looaeedr/whd/logs/preflight/20260906_t1_assembly_placement_evidence.md

SKILL_EXECUTED: phase6-corner-3d-model-integrity
READ_REFERENCE: 個人AI檔案庫/第二層_專案與SOP/06_踩坑記錄與防錯經驗庫.md
READ_REFERENCE: 基準檔/截角資料庫/README_母規則說明.md
READ_REFERENCE: 基準檔/截角資料庫/certified_relief_rules.json
READ_REFERENCE: 個人AI檔案庫/踩坑庫/phase6_assembly_relief_pitfalls.md
NOTE: T1 authoritative assembly placement contract for divider and inner door.
