looaeedr/whd/.scratch/engineering-drawing-dxf-qa/checkpoints/T3.md

# T3 Checkpoint — Canonical Annotation Planner

- ticket: #58
- branch: `feat/engineering-drawing-dxf-qa`
- tested_head: `b787f8ce18c895f643e5a339e7e7a9ddaff7f10e`
- final_remote_run: `34248282222`
- result: **6 PASS / 0 FAIL / 2.33s**
- preflight: PASS
- config.ini invariant: PASS

## Production
- `ae_engine/drawing_annotations.py`
- `ae_engine/sheetmetal_drawing.py` — preserves `ResolvedCircle.source_type`

## Test
- `tests/test_drawing_annotations.py`

## Contracts locked
- overall dimensions = Final Material bounds
- authoritative resolved-hole metadata reaches planner
- chamfer/relief measured from Final Material
- R only from stable sampled circular runs; no three-point guessing
- deterministic / immutable AnnotationPlan
- annotation does not own CUTTING/BEND/material
