looaeedr/whd/tests_analysis.md

---
whd_doc_role: REFERENCE
whd_contract: project-reference
whd_canonical: null
whd_schema: WHD_DOC_META_V1
---
# TESTS 無用性分析報告

> 運行結果：**17 failed / 402 passed**（共 57 個測試檔，419 個 test case，歷時 166 秒）

---

## 一、🔴 失敗中的「過時規格測試」（最無用）

這類測試描述的是**已不存在的 GUI 設計或已廢棄的 API 行為**，
測試本身「曾經正確」，但現在程式碼已改動，測試成了舊規格的幽靈。

### 1. `test_separate_3d_entry_contract.py` — 2 個失敗

| 測試名稱 | 失敗原因 |
|---|---|
| `test_workspace_keeps_flat_part_buttons_without_dropdown` | `workspace_part_buttons`、`workspace_part_grid` 已不存在於 gui.py |
| `test_workspace_modes_are_part_and_holes_only` | `if mode not in {"part", "holes"}` 字串已不在 gui.py |

**判斷**：測試的是已被重構掉的 workspace 設計，屬於**過期的架構合規測試**，應該刪除或更新。

---

### 2. `test_original_fold_designer_gui_integration.py` — 4 個失敗

| 測試名稱 | 失敗原因 |
|---|---|
| `test_main_gui_has_original_fold_designer_entry_and_snapshot_bridge` | `assert "corner_state" not in snap` 失敗，現在 snapshot **確實帶有** `corner_state` |
| `test_designer_result_only_writes_existing_phase6_numeric_data_and_profile_state` | 同上，寫回邏輯已更改 |
| `test_designer_endcap_result_updates_all_authoritative_endcap_vars_and_part_spec` | 邏輯改變 |
| `test_designer_apply_reloads_current_baseline_without_restoring_baseline_defaults` | 邏輯改變 |

**判斷**：測試的是 fold_designer snapshot 合約的舊版定義。snapshot 現在多了 `corner_state` / `corner_pair_same` 等欄位，這是**刻意擴充**，不是 bug，測試需要更新。

---

### 3. `test_original_fold_designer_bridge.py` — 4 個失敗

| 測試名稱 | 失敗原因 |
|---|---|
| `test_fixed_dwd_bending_ui_keeps_original_input_grid_and_disables_only_dwd_delete` | grid_slaves 中的 label 文字格式已改，`core` 標籤不再以 `str(seg["core"])` 開頭呈現 |
| `test_door_fold_edits_return_to_phase6_snapshot_without_changing_renderer_class` | `out["door_fold_l"]` 期望 23，實際 21，回寫邏輯已改 |
| `test_head_tail_preview_keeps_original_renderer_orientation` | `Poly3DCollection._vec` 屬性在新版 matplotlib 已不存在 |
| `test_head_xy_edits_export_authoritative_endcap_values_without_box_body_overwrite` | `out["fw"]` 期望 30，實際 26，映射邏輯已改 |

**判斷**：
- `_vec` 屬性問題是**第三方庫版本差異**，測試本身在 API 上假設了內部實作細節，高脆弱性。
- 其他三個是邏輯改變後測試未同步更新。

---

### 4. `test_phase6_settings_center_gui_contract.py` — 1 個失敗

| 測試名稱 | 失敗原因 |
|---|---|
| `test_apply_verifier_requires_settings_module_without_banning_corner_comboboxes` | 嘗試讀取 `apply_fold_designer_outside_dims_phase6_fix13.py`，**該檔案已不存在** |

**判斷**：測試依賴的 helper script 已刪除，這是**孤兒測試（orphan test）**，無對應實作可測。

---

### 5. `test_multi_door_gui.py` — 6 個失敗

| 測試名稱 | 失敗原因 |
|---|---|
| `test_multi_door_export_keeps_indicator_settings_owned_by_their_cell` | `BoxCalculatorGUI` 無 `add_workspace_part` 方法 |
| `test_indicator_box_and_small_door_are_same_level_workspace_parts` | `tab_indicator_box` 未加入 notebook |
| `test_single_door_indicator_box_toggle_does_not_change_multi_door_cell_modes` | 同上 |
| `test_single_door_indicator_enable_disables_indicator_box_but_keeps_box_tab_visible` | 同上 |
| `test_multi_door_editor_indicator_commit_does_not_toggle_single_door_global_mode` | `add_workspace_part` 不存在 |
| `test_indicator_box_and_small_door_are_shared_workspace_parts_and_still_in_door_editor` | 同上 |

**判斷**：測試針對 `indicator_box` 的動態 workspace 架構（`add_workspace_part`、動態 tab）撰寫，但 GUI **尚未實作這套機制**，或機制已改變。這些是**超前於實作的規格測試（spec-ahead tests）**。

---

## 二、🟡 「過度字串綁定」測試（脆弱但尚在通過）

這類測試通過 `assert '某段程式碼字串' in gui.py` 來驗證 GUI 實作，
雖然現在還通過，但**極其脆弱**：任何重構、改名、換行都會讓它無故失敗。

| 測試檔 | 問題 |
|---|---|
| `test_gui_scene_data_contract.py` | grep `gui.py` 中特定 token |
| `test_all_panel_hole_entrypoints.py` | grep `gui.py` 函式段落 |
| `test_hole_editor_ux_contract.py` | grep `gui.py` UI label 文字 |
| `test_unified_hole_catalog_contract.py` (部分) | grep `gui.py` 函式段落 |
| `test_separate_3d_entry_contract.py` (第一個) | grep gui.py — 目前通過 |
| `test_startup_door_layout_staticmethod.py` | AST parse gui.py 確認 staticmethod |
| `test_reference_axis_grouping.py` (第三個) | grep gui.py 中的 widget 名稱 |

**判斷**：這些「程式碼考古學測試」可以在不改任何功能的情況下意外失敗，維護成本高，**建議轉成行為驗證或整合測試**。

---

## 三、🟢 真正有價值的測試（保留）

### 核心幾何引擎
- `test_sheetmetal_geometry.py` — Vec2, Polygon 等幾何基礎
- `test_sheetmetal_features.py` — Feature 解析與轉換
- `test_sheetmetal_drawing.py` — DXF primitive 構建
- `test_strip_fold_chain.py` — BEND 位置數學
- `test_four_side_flange_geometry.py` — FourSideFlange
- `test_corner_types.py` — CornerType snapshot regression

### 零件適配器
- `test_sheetmetal_part_adapters.py` — 門、封頭尾、底板適配
- `test_multi_door_layout.py` — 多門尺寸計算邏輯
- `test_endcap_head_mirror.py` — 封頭鏡像

### DXF 輸出管線
- `test_ae_dispatcher.py` — `_build_*_scene` 各零件
- `test_manufacturing_api.py` — generate_part 整合
- `test_manufacturing_policy_boundary.py` — Policy 注入
- `test_manufacturing_api_finished_face_contract.py`
- `test_corner_type_headless.py` — 無 GUI 的 corner type 輸出

### 孔洞系統
- `test_hole_catalog.py`
- `test_hole_rotation.py`
- `test_unified_hole_reference.py`
- `test_feature_surface.py`
- `test_unified_hole_process_toggle.py`
- `test_profile_layer_preservation.py`
- `test_round_hole_pattern.py`

### 架構合規（仍有效）
- `test_clean_break_layout.py` — 確認無舊根目錄模組
- `test_ae_engine_package.py` — 確認 ae_engine 套件完整性

---

## 四、總結建議

| 分類 | 數量 | 建議 |
|---|---|---|
| 🔴 **立即可刪除 / 應更新**（失敗中的過期測試） | ~17 個 case | 更新或刪除 |
| 🟡 **脆弱字串綁定測試**（通過但易斷） | ~10 個 case | 重構為行為測試 |
| 🟢 **真正有價值** | ~392 個 case | 保留 |

### 最優先處理的 3 個動作
1. **刪除** `test_phase6_settings_center_gui_contract.py::test_apply_verifier_requires_settings_module_without_banning_corner_comboboxes`（依賴已不存在的檔案）
2. **更新** `test_original_fold_designer_gui_integration.py` 前兩個失敗測試（snapshot 合約已合法擴充）
3. **評估** `test_multi_door_gui.py` 的 `indicator_box` 系列 —— 若 `add_workspace_part` 機制尚未實作，這些測試是 **spec-ahead**，應先暫時 `@pytest.mark.xfail` 或移至 backlog

## Headless / Xvfb 測試判讀規則（CURRENT）

1. 無 `DISPLAY`：pure/headless tests 必須跑；GUI/Tk tests 應 SKIP，不得把缺 display 的 `TclError` 當功能紅燈。
2. 有 Xvfb：GUI/Tk tests 必須真的執行；任何 geometry/state/save-reload failure 都是有效紅燈，不能以 headless skip 掩蓋。
3. 新 GUI tests 使用 `@pytest.mark.requires_tk_display`。中央兼容層只辨識「缺 DISPLAY」的 Tk `TclError`，不吞其他 TclError。
4. Release gate 必須同時保留 headless 與 Xvfb 證據；只跑其中一種不得宣稱正式 GUI release 通過。
