looaeedr/whd/.scratch/engineering-drawing-dxf-qa/T1.state.md

# T1 State
- task_id: engineering-drawing-dxf-qa
- ticket: #57
- role: QA Accepted
- branch: feat/engineering-drawing-dxf-qa
- baseline_sha: 55541aaef49c3bb5649f52160a87a2834c1072a9
- requirement_red_run_id: 34244926280
- requirement_red_head_sha: 9f92663f1554d93c7af462db89d3283825f6d5f4
- requirement_red_result: 2 failed / valid requirement RED
- final_green_run_id: 34246080067
- final_tested_head_sha: e1eac5a16258f15f805468362390f30020ad6fff
- final_green_result: 8 passed / 0 failed / 1.15s
- config_ini_invariant: PASS
- py_compile: PASS
- cleanup_head_sha: 58ac96e403d8ad43fefa494a8396620f45dfdeca
- workflow_cleanup: PASS / .github/workflows/t1-dxf-acceptance.yml removed
- drift_audit: PASS / production+test blobs identical tested-head→cleanup-head
- status: ACCEPTED
- completed: independent saved-DXF verifier; layer mismatch; CUTTING mismatch; hole/extra geometry checks; public manufacturing seam; AI Library writeback; focused remote QA; workflow cleanup; drift audit
- blocked: none
- production_files: ae_engine/dxf_acceptance.py; ae_engine/manufacturing_api.py
- test_files: tests/test_dxf_acceptance.py; tests/test_resolved_manufacturing_export.py
