looaeedr/whd/.scratch/engineering-drawing-dxf-qa/T2.state.md

# T2 State
- task_id: engineering-drawing-dxf-qa
- ticket: #59
- role: T2 Implementer -> QA Review
- branch: feat/engineering-drawing-dxf-qa
- baseline_sha: 65d34a6b2a43c12bf415a5f2f1e87a270e4c751a
- blocker: #57 CLOSED / ACCEPTED
- requirement_red_run_id: 34246552158
- requirement_red_result: 3 failed / 8 passed / valid R4 RED
- final_green_run_id: 34246933143
- final_green_tested_head_sha: 065bd0b54fbe47cc12908e128235bcb5b163052a
- final_green_result: 11 passed / 0 failed / py_compile PASS / config.ini invariant PASS
- workflow_cleanup_sha: 45ac45bf2b18fa01c19b845a726ab7bca30b9d97
- checkpoint_path: .scratch/engineering-drawing-dxf-qa/checkpoints/T2.md
- status: ACCEPTED
- completed: stable physical IDs; group reopen verifier; missing/extra file-set detection; filename identity policy; AI Library writeback; terminal remote QA; workflow cleanup
- pending: none
- blocked: none
- resume_command: inspect #59 and checkpoint T2.md
- drift_audit: PASS / tested head 065bd0b54fbe47cc12908e128235bcb5b163052a → pre-close head 92923c63036cc85d88bdc6bf400a9e9e318cf501; 5 production/test blobs identical
