looaeedr/whd/.scratch/engineering-drawing-dxf-qa/T3.state.md

# T3 State
- task_id: engineering-drawing-dxf-qa
- ticket: #58
- role: T3 Implementer -> QA Review
- branch: feat/engineering-drawing-dxf-qa
- baseline_sha: 2dc2103eb872c377a3e28ea4ed57907d1e004382
- requirement: R1 canonical Annotation Planner
- valid_requirement_red_run_id: 34247464567
- valid_requirement_red_head_sha: 98e03ac2e91c974057c1b39ac0559b7830334625
- valid_requirement_red_result: 4 failed / explicit R1 assertions
- radius_red_run_id: 34247880052
- radius_red_head_sha: 2cb4e58a72f4a3e4ac703ff1d9a69cd38db7b0fd
- radius_red_result: 1 failed / 4 passed
- metadata_red_run_id: 34248187080
- metadata_red_head_sha: aa49bae8cbea51daa507f59a2aac737f6e83e33d
- metadata_red_result: 1 failed / 5 passed
- final_green_run_id: 34248282222
- final_tested_head_sha: b787f8ce18c895f643e5a339e7e7a9ddaff7f10e
- final_green_result: 6 passed / 0 failed / 2.33s
- preflight: PASS
- config_ini_invariant: PASS
- status: QA_REVIEW
- completed: overall dimensions from final material; authoritative hole callouts; corner relief callouts; stable R callouts; deterministic/immutable plan; ResolvedCircle source metadata preservation; AI Library writeback; final remote QA terminal success
- pending: workflow cleanup readback; drift audit; owning Issue terminal evidence / close
- blocked: none
- production_files: ae_engine/drawing_annotations.py; ae_engine/sheetmetal_drawing.py
- test_file: tests/test_drawing_annotations.py
