looaeedr/whd/.scratch/engineering-drawing-dxf-qa/T4.preflight.evidence.md

T4 Annotation Collision Resolver preflight evidence
phase6-corner-3d-model-integrity
tdd
diagnosing-bugs
monitoring-remote-qa
READ_REFERENCE: 個人AI檔案庫/第二層_專案與SOP/06_踩坑記錄與防錯經驗庫.md
READ_REFERENCE: 個人AI檔案庫/第二層_專案與SOP/04_WHD鈑金展開幾何引擎規範.md
READ_REFERENCE: handoff/04_DEVELOPMENT_RULES.md
READ_REFERENCE: 基準檔/截角資料庫/README_母規則說明.md
READ_REFERENCE: 基準檔/截角資料庫/certified_relief_rules.json
READ_REFERENCE: 個人AI檔案庫/踩坑庫/phase6_assembly_relief_pitfalls.md
