looaeedr/whd/.scratch/engineering-drawing-dxf-qa/T4.state.md

# T4 State
- task_id: engineering-drawing-dxf-qa
- ticket: #60
- role: QA Accepted
- branch: feat/engineering-drawing-dxf-qa
- baseline_sha: 0b4adb92a5fc5fffa8600a0328c7e9255223f21f
- blocker: #58 CLOSED / ACCEPTED
- requirement: R2 deterministic annotation collision resolver
- initial_requirement_red_run_id: 34249387413
- initial_requirement_red_head_sha: 3a89ea5421a7885bb90ffa2529b5de9e4cd83709
- initial_requirement_red_result: 1 failed / explicit missing R2 resolver assertion
- manufacturing_obstacle_red_run_id: 34249693238
- manufacturing_obstacle_red_result: 1 failed / 2 passed
- annotation_text_red_run_id: 34249858548
- annotation_text_red_result: 1 failed / 3 passed
- dimension_line_red_run_id: 34250034870
- dimension_line_red_result: 1 failed / 4 passed
- introduced_bug_run_id: 34250144100
- introduced_bug_classification: INVALID_AS_REQUIREMENT_RED / UnboundLocalError axis-before-assignment
- helper_intermediate_run_id: 34250484170
- helper_intermediate_classification: NON_ACCEPTANCE / helper-only head / 1 failed + 5 passed
- leader_strict_red_run_id: 34250338340
- leader_strict_red_result: 1 failed / 5 passed
- final_green_run_id: 34250724434
- final_tested_head_sha: 4a978507f81c51ff5e54aa4d0c59451ac7ab3823
- final_green_result: 13 passed / 0 failed / 0.63s
- preflight: PASS
- py_compile: PASS / drawing_annotations + drawing_annotation_layout + sheetmetal_drawing
- config_ini_invariant: PASS
- status: ACCEPTED
- completed: deterministic axis-constrained dimensions; CUTTING/BEND/hole obstacle extraction; annotation text/dimension self-avoidance; TITLE/TECH reserved regions; callout leader placement; unresolved diagnostics; strict failure; combined T3+T4 regression; AI Library writeback
- pending: none
- blocked: none
- production_files: ae_engine/drawing_annotation_layout.py
- upstream_guard_files: ae_engine/drawing_annotations.py; ae_engine/sheetmetal_drawing.py
- test_files: tests/test_annotation_collision_resolver.py; tests/test_drawing_annotations.py
- cleanup_head_sha: 7625b8586e08b7c550f9da4f6ee6405f46a0f24f
- workflow_cleanup: PASS / focused workflow removed and remote-read absent
- drift_audit: PASS / 5 production-test blobs identical tested-head→cleanup-head
