looaeedr/whd/.scratch/engineering-drawing-dxf-qa/T5.preflight.evidence.md

T5 2D / Engineering Drawing integration preflight evidence
tdd
diagnosing-bugs
monitoring-remote-qa
READ_REFERENCE: 個人AI檔案庫/第二層_專案與SOP/04_WHD鈑金展開幾何引擎規範.md
READ_REFERENCE: 個人AI檔案庫/第二層_專案與SOP/06_踩坑記錄與防錯經驗庫.md
READ_REFERENCE: handoff/04_DEVELOPMENT_RULES.md
