looaeedr/whd/.scratch/engineering-drawing-dxf-qa/T5.state.md

# T5 State
- task_id: engineering-drawing-dxf-qa
- ticket: #61
- role: QA Accepted
- branch: feat/engineering-drawing-dxf-qa
- baseline_sha: 836de5c2e589dc300c10b0e15220d1e243454fd8
- blockers: #58 CLOSED / #60 CLOSED
- requirement: R1/R2 2D + Engineering Drawing integration
- r1_red_run_id: 34251681198
- r1_red_head_sha: d2182631f89565f3638ef5f0827e70a041cc007e
- r1_red_result: 2 failed / shared Engineering Drawing seam missing + 6/6 primary 2D previews bypass AnnotationPlan
- r1_green_run_id: 34252792624
- r1_green_result: 4 passed / 0 failed
- r2_red_run_id: 34253016841
- r2_red_head_sha: 89de76ef757f405156c234a023f479a173f4cb5f
- r2_red_result: 2 failed / 4 passed / shared finished provider missing + 6/6 2D previews bypass finished summary
- r2_harness_runs: 34253175734, 34253218116, 34253241070, 34253284565, 34253307500
- r2_harness_classification: NON-ACCEPTANCE / matplotlib import dependency in source-ownership test; later heads had 5 passing behavioral guards
- r2_green_run_id: 34253442671
- r2_green_result: 6 passed / 0 failed
- behavior_guard_run_id: 34253559918
- behavior_guard_result: 8 passed / 0 failed
- parity_guard_run_id: 34253660862
- parity_guard_result: SUCCESS
- final_green_run_id: 34253680763
- final_tested_head_sha: 33462e78a282a3999f29abd1a3673a106a78f999
- final_green_result: 22 passed / 0 failed / 4.63s
- preflight: PASS
- py_compile: PASS / planner + collision + engineering projection + display dimensions + 3D view + bridge + GUI
- config_ini_invariant: PASS
- completed: shared AnnotationPlan projection; 6 primary 2D previews integrated; handwritten overall W/H removed; manufacturing DXF separation; shared 2D/3D finished-dimension provider; folded mesh priority; box-body 400x596x250 parity; family-switch stale-ID guard
- ai_library_writeback: DONE
- status: ACCEPTED
- pending: none
- blocked: none
- production_files: ae_engine/engineering_drawing.py; ae_engine/display_dimensions.py; gui.py; fold_designer_bridge.py; phase6_final_scene_view.py
- test_files: tests/test_engineering_drawing_integration.py; tests/test_drawing_annotations.py; tests/test_annotation_collision_resolver.py
- cleanup_head_sha: 1cb592beed4b03031bbe4db08f01cada67d48111
- workflow_cleanup: PASS / focused workflow removed and remote-read absent
- drift_audit: PASS / 10 production-test blobs identical tested-head→cleanup-head
