looaeedr/whd/.scratch/engineering-drawing-dxf-qa/T6.preflight.evidence.md

# T6 Combined Acceptance Preflight Evidence

- task: T6 Combined Acceptance — DXF reopen / multipart Receiving Divider / Vault / Save-Reload / engineering annotation / remote QA
- repository: looaeedr/whd
- branch: feat/engineering-drawing-dxf-qa
- integrated_head: bb8e495983e4c0da27724c0809bb7c52f86ba4b9
- integration_parents: 521a166dc5ef0b002646587a60c373fa95a52818 + b8f08cfbf6fa83617135da70648c946aefe74bd4

READ_SKILL: phase6-corner-3d-model-integrity
READ_SKILL: phase6-overlay-relief-basis
READ_SKILL: diagnosing-bugs
READ_SKILL: tdd
READ_SKILL: monitoring-remote-qa
READ_SKILL: 掃描深模組

READ_REFERENCE: 個人AI檔案庫/第二層_專案與SOP/04_WHD鈑金展開幾何引擎規範.md
READ_REFERENCE: 個人AI檔案庫/第二層_專案與SOP/06_踩坑記錄與防錯經驗庫.md
READ_REFERENCE: handoff/04_DEVELOPMENT_RULES.md
READ_REFERENCE: 基準檔/截角資料庫/README_母規則說明.md
READ_REFERENCE: 基準檔/截角資料庫/certified_relief_rules.json
READ_REFERENCE: 個人AI檔案庫/踩坑庫/phase6_assembly_relief_pitfalls.md
READ_CONTEXT: CONTEXT.md

## Combined hard gates
- T1–T5 terminal evidence already closed/accepted.
- Issue63 accepted production must be present in the same tested branch before Combined.
- Receiving multipart physical pieces are ownership/collision authority.
- Divider fixed-hole source datum comes from 中隔.dxf fixed features, never its outer contour.
- Validation values are not production calculation inputs; no magic 174 / 47-26 / 100 / 1mm / bbox/probe oracle.
- production DXF remains canonical manufacturing scene only.
- Engineering Drawing remains annotation-only downstream projection.
- Save→Reload must preserve canonical state and Final Material.
- config.ini SHA256 must remain identical.
