looaeedr/whd/.scratch/engineering-drawing-dxf-qa/T6.state.md

# T6 State
- task_id: engineering-drawing-dxf-qa
- ticket: #62
- role: QA Accepted
- branch: feat/engineering-drawing-dxf-qa
- original_baseline_sha: 55541aaef49c3bb5649f52160a87a2834c1072a9
- t1_t5_head_before_issue63_merge: 521a166dc5ef0b002646587a60c373fa95a52818
- issue63_closing_head: b8f08cfbf6fa83617135da70648c946aefe74bd4
- integrated_head: bb8e495983e4c0da27724c0809bb7c52f86ba4b9
- integration_commit_type: two-parent merge
- integration_parents: 521a166dc5ef0b002646587a60c373fa95a52818 + b8f08cfbf6fa83617135da70648c946aefe74bd4
- combined_run_id: 34254984310
- combined_tested_head_sha: f39398c1fbd3e50e26b5fc8453729c52bfef135e
- combined_status: completed / success
- core_dxf_annotation: 39 PASS / 0 FAIL
- receiving_issue63_suite: 91 PASS / 0 FAIL
- vault_save_reload: 45 PASS / 0 FAIL
- combined_total: 175 PASS / 0 FAIL
- preflight: PASS
- py_compile: PASS
- source_ownership_guards: PASS
- config_ini_before: 980eab68d4a1732a5313b22329852dfc9691c83e4e2a64cccd18022afae4ee67
- config_ini_after: 980eab68d4a1732a5313b22329852dfc9691c83e4e2a64cccd18022afae4ee67
- config_ini_invariant: PASS
- blockers: #57 CLOSED / #58 CLOSED / #59 CLOSED / #60 CLOSED / #61 CLOSED / #63 CLOSED
- ai_library_writeback: DONE + REREAD
- skill_writeback: phase6-corner-3d-model-integrity DONE + REREAD
- status: ACCEPTED
- pending: none
- blocked: none
- workflow_cleanup: PASS / t6-combined-acceptance.yml removed and remote-read absent
- first_drift_audit_head: 5b515c23ad00194c0b30d7f9393b3dbf0316514c
- first_drift_audit: PASS / only AI-Skill-state-checkpoint-workflow cleanup files changed
- validation_docs_target_head: a26d14f524ff4c094afd4718fc61679db663f847
- validation_docs_merge_head: 9a0acc9315519afbb128d0f8e09c053f336439f1
- validation_docs_merge: PASS / two-parent docs-only merge / production-test drift 0
- target_integration_head: 69ede1f29af9f97b3bed1b844478f40fc251f347
- target_integration: PASS / cleanup/2d-3d-sync non-force fast-forward / remote reread identical
- final_production_test_drift: PASS / 0 files changed after tested head
- tracker_close: PASS / #62 closed
- final_target_head: 34cb7975cc4bad8d0102c52884265739412e8139
