looaeedr/whd/.scratch/validation-authority-boundary/phase6_preflight_evidence.md

# Validation Authority Boundary — Phase6 Preflight Evidence

- task: 驗證只能拿來判定對不對，不能反過來當 production 計算來源；加入 Skill 與 AI Library
- repository: looaeedr/whd
- branch: docs/validation-authority-boundary
- parent: cleanup/2d-3d-sync@b8f08cfbf6fa83617135da70648c946aefe74bd4

READ_SKILL: phase6-release-packaging
READ_SKILL: phase6-corner-3d-model-integrity
READ_SKILL: tdd

READ_REFERENCE: 個人AI檔案庫/第二層_專案與SOP/06_踩坑記錄與防錯經驗庫.md
READ_REFERENCE: release_required_artifacts.json
READ_REFERENCE: 個人AI檔案庫/踩坑庫/phase6_assembly_relief_pitfalls.md

## RED baseline
- phase6-corner-3d-model-integrity explicit "validation is not calculation source": false
- explicit ban on pytest expected/tolerance feeding production: false
- explicit ban on validation measurement backfeed: false

## Scope expansion
- Added general TDD authority boundary after locating the project-wide tdd Skill.

## Intended files
- .agents/skills/engineering/tdd/SKILL.md
- .agents/skills/engineering/phase6-corner-3d-model-integrity/SKILL.md
- 個人AI檔案庫/第二層_專案與SOP/06_踩坑記錄與防錯經驗庫.md
- 個人AI檔案庫/踩坑庫/phase6_assembly_relief_pitfalls.md

## Remote preflight terminal evidence
- run_id: 34254285308
- head_sha: 89f7017726e0f51bbf3ea51c9730beeaf23541a1
- conclusion: completed / success
- report: phase6-release-packaging ✓; global pitfalls ✓; release_required_artifacts.json ✓
- scope-expansion run_id: 34254488598
- head_sha: b1654e7523dd94042e3dd0016cf7745d17482fe7
- conclusion: completed / success

## GREEN content contract
- tdd one-way validation authority: PASS
- phase6-corner-3d-model-integrity validation/calculation boundary: PASS
- global AI Library boundary: PASS
- phase6 assembly/relief AI Library boundary: PASS
- expected/fixture/probe/tolerance backfeed ban: PASS
- independent authoritative provenance requirement: PASS
- production/test source drift: 0 production files, 0 test files

## Closing audit
- one-shot workflow cleanup: PASS
- accidental rerun after workflow deletion: none
- production files changed: 0
- test files changed: 0
- target before integration: cleanup/2d-3d-sync@b8f08cfbf6fa83617135da70648c946aefe74bd4
- pre-evidence closing commit: d747c563e24d0a3f9bddbb03391587461fa15d4b
- integration mode: non-force fast-forward only
