looaeedr/whd/logs/preflight/20260906_remote_qa_monitoring_evidence.md

# Remote QA Monitoring Skill Preflight Evidence

Task: 增加規則：同步遠端 QA 時必須啟動監控技能，並持續追到遠端 QA 終態。
Date: 2026-09-06

READ_SKILL: phase6-release-packaging
READ_SKILL: dispatching
READ_SKILL: monitoring-remote-qa
READ_REFERENCE: 個人AI檔案庫/第二層_專案與SOP/06_踩坑記錄與防錯經驗庫.md
READ_REFERENCE: .agents/skills/skill_registry.json
READ_REFERENCE: tools/phase6_skill_preflight.py
READ_REFERENCE: release_required_artifacts.json

Planned files:
-  .agents/skills/engineering/monitoring-remote-qa/SKILL.md
-  .agents/skills/engineering/monitoring-remote-qa/agents/openai.yaml
- .agents/skills/skill_registry.json
- .agents/skills/engineering/派工/SKILL.md
- .agents/skills/engineering/README.md
- AGENTS.md

RESULT: PRE-FLIGHT READ COMPLETE
POST-CREATE READBACK: monitoring-remote-qa SKILL.md verified

REMOTE QA CONTRACT: 22 PASS / 0 FAIL (run 34022265417)
ROUTE/WIRING CHECK: PASS (run 34022430582)
CANONICAL SKILL: monitoring-remote-qa
TEMP SELF-TEST WORKFLOW: removed
