looaeedr/whd/logs/preflight/20260906_remote_qa_monitoring_skill_evidence.md

# Remote QA Monitoring Skill Preflight Evidence

READ_SKILL: phase6-release-packaging
READ_SKILL: diagnosing-bugs
READ_SKILL: tdd
READ_SKILL: monitoring-remote-qa
READ_SKILL: superpowers/writing-skills
READ_SKILL: superpowers/test-driven-development
READ_REFERENCE: 個人AI檔案庫/第二層_專案與SOP/06_踩坑記錄與防錯經驗庫.md
READ_REFERENCE: release_required_artifacts.json
RED: tests/test_remote_qa_monitoring_skill_contract.py -> 1 failed (skill missing)
GREEN: tests/test_remote_qa_monitoring_skill_contract.py -> 1 passed
PREFLIGHT: PASS
