looaeedr/whd/logs/preflight/20260906_t10_release_verification_evidence.md

# T10 Release Verification Evidence

phase6-corner-3d-model-integrity
phase6-release-packaging
diagnosing-bugs
tdd
dispatching
READ_REFERENCE: 個人AI檔案庫/第二層_專案與SOP/06_踩坑記錄與防錯經驗庫.md
READ_REFERENCE: 基準檔/截角資料庫/README_母規則說明.md
READ_REFERENCE: 基準檔/截角資料庫/certified_relief_rules.json
READ_REFERENCE: 個人AI檔案庫/踩坑庫/phase6_assembly_relief_pitfalls.md
READ_REFERENCE: release_required_artifacts.json

## Scope
- Issue: #10 高風險完整 Headless + GUI Gate / Release Verification
- T10 start commit: 60fb7a935cd078c38e81d5ad6175fa42b0cc66ce
- Execution tree SHA: 51c1454ea64284f204c286c3876e92b2ff4daa1d
- Backup: backup-20260906-110833
- Headless journal: logs/release_gate/t10_phase6_headless.jsonl
- Xvfb journal: logs/release_gate/t10_phase6_xvfb.jsonl

## Durable Release Gate
- Collection count: 1473 nodeids in both modes.
- Collection SHA256: 14db2438f4285b64eb396a5744986104a02a9135cfcefcfbb12de72ecaeb269c.
- Headless: completed=1473, passed=1194, skipped=279, failed_batches=0, pending=0, teardown_timeout_batches=0.
- Xvfb: completed=1473, passed=1473, skipped=0, failed_batches=0, pending=0, teardown_timeout_batches=2.
- Xvfb aggregate timeout records: 4; every timed-out nodeid was later recorded complete in the same durable journal; unresolved timeout nodeids=0.
- The 2 complete_teardown_timeout batches each have full `20 passed` pytest summaries and are classified complete by `phase6-release-packaging` policy, not as production failures.

## Integrity Guards
- config.ini SHA256 current: e0d8e0c9a6db736f1f7882ff2246cb2845467431bafa583f81a35a0e1d551dc5.
- config.ini SHA256 at T10 start: e0d8e0c9a6db736f1f7882ff2246cb2845467431bafa583f81a35a0e1d551dc5.
- No production or test source changed during T10; only checkpoint/evidence/release-journal artifacts changed after T10 start.
- No unresolved pytest/Xvfb child process is accepted as release evidence; final orphan check is part of final verification.

## Packaging Boundary
- T10 release-verification artifact is the durable checkpoint/evidence bundle.
- No formal FULL/UPDATE ZIP is generated in this task because no explicit runtime baseline FULL ZIP was supplied. The project release skill explicitly forbids guessing a historical/latest baseline.

## Final Gate
- Status: GATE_COMPLETE_FINAL_PREFLIGHT_GREEN
- Completion rule: final preflight green; checkpoint ZIP CRC/UTF-8 paths clean; modification log appended; worktree clean; GitHub push verified.

- Final Phase6 Preflight: PASS (phase6-corner-3d-model-integrity, phase6-release-packaging, 5/5 required references).
