looaeedr/whd/.scratch/engineering-drawing-dxf-qa/checkpoints/T1.md

# T1 Checkpoint — DXF Output-Reopen Acceptance

- ticket: #57
- branch: feat/engineering-drawing-dxf-qa
- baseline_sha: 55541aaef49c3bb5649f52160a87a2834c1072a9
- tested_head_sha: e1eac5a16258f15f805468362390f30020ad6fff
- workflow_cleanup_sha: 58ac96e403d8ad43fefa494a8396620f45dfdeca
- requirement_red_run: 34244926280 (2 failed, valid requirement RED)
- final_green_run: 34246080067 (8 passed / 0 failed)
- config_ini_invariant: PASS
- py_compile: PASS
- workflow_cleanup: PASS

## Provenance
- ae_engine/dxf_acceptance.py: e9f23dba4a64fb47dcfece83f4b04cde6b8402bd
- ae_engine/manufacturing_api.py: 89b2f3ceb4e99c48895188377d0b3802ba4dbd84
- tests/test_dxf_acceptance.py: ac651f43fafd0f4b76d613425e76ef32b8b515cd
- 個人AI檔案庫/第二層_專案與SOP/04_WHD鈑金展開幾何引擎規範.md: 9cfc5cabb92a8b0344790704d81dc78099b900c5
- 個人AI檔案庫/第二層_專案與SOP/06_踩坑記錄與防錯經驗庫.md: 2ad738bd59f406f5309fec8994e9391906e446d0

## Acceptance
- exact round-trip PASS
- removed BEND detected
- wrong layer detected as LAYER_MISMATCH
- CUTTING shape mutation detected
- removed CUTTING hole detected
- extra BEND detected
- existing resolved manufacturing export guards PASS
- serializer ownership unchanged
