looaeedr/whd/.scratch/engineering-drawing-dxf-qa/checkpoints/T2.md

# T2 Checkpoint — Multipart / Dynamic Physical-Part DXF Acceptance

- ticket: #59
- branch: feat/engineering-drawing-dxf-qa
- baseline_sha: 65d34a6b2a43c12bf415a5f2f1e87a270e4c751a
- tested_head_sha: 065bd0b54fbe47cc12908e128235bcb5b163052a
- current_head_sha: 45ac45bf2b18fa01c19b845a726ab7bca30b9d97
- requirement_red_run: 34246552158 (3 failed / 8 passed; valid R4 RED)
- final_green_run: 34246933143 (11 passed / 0 failed)
- py_compile: PASS
- config_ini_invariant: PASS
- workflow_cleanup_sha: 45ac45bf2b18fa01c19b845a726ab7bca30b9d97

## Provenance
- ae_engine/manufacturing_api.py: 9c4a407dcc33fcc6cad210447eec2d5873d57b59
- ae_engine/dxf_acceptance.py: 8aeacf36c2f21ef794c8278f1a396eed6e0e8d91
- tests/test_multipart_dxf_acceptance.py: 2b2b5caeeec9e77fd6bd2ddd95acdbf9c216743f
- 個人AI檔案庫/第二層_專案與SOP/04_WHD鈑金展開幾何引擎規範.md: 66a1121a64aaf22392e3d500cf93da8665839638
- 個人AI檔案庫/第二層_專案與SOP/06_踩坑記錄與防錯經驗庫.md: c5a5895b0209f371bed1863c332609dd0a532392

## Acceptance
- Box Body physical IDs use manufacturing piece key/role, not collection index
- Receiving-style left_side/back/right_side export as stable domain IDs
- physical-piece filenames remain distinct from dynamic part filenames
- every expected physical part is reopened and independently verified
- missing physical DXF -> MISSING_PART
- stale/extra DXF -> EXTRA_PART
- dynamic divider / door IDs included in acceptance set
- existing T1 saved-DXF acceptance and resolved export guards remain GREEN
