looaeedr/whd/.scratch/engineering-drawing-dxf-qa/checkpoints/T4.md

# T4 Checkpoint — Annotation Collision Resolver

- ticket: #60
- branch: `feat/engineering-drawing-dxf-qa`
- baseline: `0b4adb92a5fc5fffa8600a0328c7e9255223f21f`
- tested_head: `4a978507f81c51ff5e54aa4d0c59451ac7ab3823`
- final_remote_run: `34250724434`
- result: **13 PASS / 0 FAIL / 0.63s**
- preflight: PASS
- py_compile: PASS
- config.ini invariant: PASS

## Production
- `ae_engine/drawing_annotation_layout.py`

## Guards
- `ae_engine/drawing_annotations.py`
- `ae_engine/sheetmetal_drawing.py`
- `tests/test_drawing_annotations.py`
- `tests/test_annotation_collision_resolver.py`

## Contracts locked
- deterministic annotation layout
- horizontal dimension text moves X only
- vertical dimension text moves Y only
- avoids CUTTING / BEND / holes / other dimensions / text / TITLE / TECH regions
- manufacturing DrawingScene stays immutable
- legal callout moves and gets annotation-only leader
- unresolved callout => UNRESOLVED_LEADER diagnostic
- strict unresolved collision => FAIL
