looaeedr/whd/.scratch/engineering-drawing-dxf-qa/checkpoints/T5.md

# T5 Checkpoint — 2D / Engineering Drawing Integration

- ticket: #61
- branch: `feat/engineering-drawing-dxf-qa`
- baseline: `836de5c2e589dc300c10b0e15220d1e243454fd8`
- tested_head: `33462e78a282a3999f29abd1a3673a106a78f999`
- final_remote_run: `34253680763`
- result: **22 PASS / 0 FAIL / 4.63s**
- preflight: PASS
- py_compile: PASS
- config.ini invariant: PASS

## Production
- `ae_engine/engineering_drawing.py`
- `ae_engine/display_dimensions.py`
- `gui.py`
- `fold_designer_bridge.py`
- `phase6_final_scene_view.py`

## Contracts locked
- six primary 2D previews consume shared AnnotationPlan projection
- Engineering Drawing projection is annotation-only
- production manufacturing DXF serializes original render_data.scene only
- 2D/3D share one finished-dimension provider
- folded mesh envelope wins over snapshot fallback
- box-body 400 × 596 × 250 fallback parity preserved
- family/baseline switch cannot retain stale feature IDs
