looaeedr/whd/.scratch/engineering-drawing-dxf-qa/checkpoints/T6.md

# T6 Checkpoint — Combined Acceptance

- ticket: #62
- branch: `feat/engineering-drawing-dxf-qa`
- combined tested head: `f39398c1fbd3e50e26b5fc8453729c52bfef135e`
- integrated ancestry head: `bb8e495983e4c0da27724c0809bb7c52f86ba4b9`
- integration parents:
  - T1–T5: `521a166dc5ef0b002646587a60c373fa95a52818`
  - Issue63: `b8f08cfbf6fa83617135da70648c946aefe74bd4`
- remote run: `34254984310`
- result: **175 PASS / 0 FAIL**
  - Core DXF/Annotation: 39
  - Receiving/Issue63: 91
  - Vault/Save→Reload: 45
- Preflight: PASS
- py_compile: PASS
- source ownership guards: PASS
- config.ini: `980eab68...` before = after

## Integration gate
T1–T5 and Issue63 were initially diverged. Combined QA was not allowed until a real two-parent merge made both accepted histories ancestors of the same tested branch.

## Permanent writeback
- AI Library: Combined ancestry gate + validation-not-calculation-source rule.
- Skill: `phase6-corner-3d-model-integrity` now carries the same hard gates.
