looaeedr/whd/個人AI檔案庫/踩坑庫/continuous_execution_pitfalls.md

---
whd_doc_role: REFERENCE
whd_contract: continuous-execution-operations
whd_canonical: null
whd_schema: WHD_DOC_META_V1
---

# 長流程持續執行 / 停工點踩坑規則

> **[REFERENCE — FLOW V2 CURRENT SEMANTICS ONLY]** 本檔保留大量 pre-Flow-v2 checkpoint / continuity-controller 事故敘述。凡出現 `tools/continuity_controller.py`、`RECOVERING checkpoint`、legacy work-order branch、claim/Guard/finalization 等 imperative wording，除非段落明確標 CURRENT Flow v2，均只作 historical evidence；不得覆蓋 `.agents/skills/engineering/flow-v2-execution/SKILL.md`。

## SCHEDULED_WAKEUP_STATUS_ONLY_PITFALL

排程／automation 只是 wake-up trigger，不是 execution owner；canonical shorthand：`wake-up trigger != execution owner`。醒來後只做狀態回報再停止，等同把排程誤當 execution cadence，屬於 continuity regression。

- 先恢復 owning issue/checkpoint/branch/current concrete RUN identity。
- 有 concrete RUN：沿 canonical remote-QA contract 追到 terminal，然後直接進下一個 autonomous step。
- 沒有 concrete RUN 但 owning plan 需要 RUN：分類 `RUN_NOT_CREATED`，立即處理會建立 RUN 的 prerequisite/trigger/fix，禁止等待。
- `status update != exit`；GREEN/RED 都不是自動停點。
- 若平台被迫切斷，先留下完整 durable checkpoint，下一次 wake-up 從 exact next action 恢復。
- 本段是 REFERENCE/pitfall；唯一 scheduled-wakeup execution authority 是 `flow-v2-execution` 的 ExecutionRecord + scheduler view + invocation-exit machine。`executable-continuity-controller` 舊名稱只作 registry retired alias；filesystem Skill shim 已移除。

## Authority status

本文件只保留歷史事故、操作提醒與相容性回歸背景，角色是 **REFERENCE**，不是 executable authority。

- executable semantic CURRENT：`WHD_EXECUTION_RECORD_V2` + `tools/control_transaction.py` + `tools/execution_invocation_exit.py`。
- operational CURRENT：`.agents/skills/engineering/flow-v2-execution/SKILL.md`。
- legacy continuity runtime 已從 CURRENT tree 移除；`executable-continuity-controller` 只保留 retired alias 與 historical provenance，marker/string presence 不是 executable enforcement。
- 本文件若與 Flow v2 CURRENT authority 衝突，以 Flow v2 為準；不得從舊 checkpoint marker、字串或舊 test 反推 machine state/finalization 行為。

## 事故模式：把派工完成當成停工點

WHD 曾發生：Master 與子工單已建立、第一張可執行子工單也已明確，但 AI 以「派工完成」作為回覆終點，把後續實作留給使用者再輸入「繼續」。這是流程缺陷，不是正常 checkpoint。

## 永久規則

- **進度回報不是工作終點。** branch created、issue created、commit/push、QA started、run_id acquired、focused PASS、下一步明確，都只是中間態。
- 只要**存在可自主執行的下一步**，且沒有真正 blocker / Runtime interruption，就必須在同一工作流程繼續執行；不得輸出 terminal/final 狀態把控制權交回使用者。
- **使用者不是續跑 scheduler。** 不得依賴使用者再輸入「繼續」「輪」「跑」「continue」「poll」才讓既有非終態工作前進。
- Gate RED / preflight FAIL 是 fail-closed boundary：禁止越過受保護階段，但仍要繼續完成 Gate 所要求的 evidence、readback 或修復，直到 GREEN 或出現真正 blocker。
- Test / QA FAIL 可自行診斷時要進 recovery：evidence → root cause → minimal fix → validation → retry；FAIL 本身不是停工理由。
- 只有 COMPLETE、真正需要產品決策/權限/不可推導資料的 BLOCKED，或平台實際 Runtime/tool interruption，才允許離開目前工作鏈。
- Runtime 被硬切時要留下 durable checkpoint；下一回合先驗 drift，再從 next exact action 續跑，不重新要求使用者交代已知上下文。

以上是 reference guidance；CURRENT durable state、transition、resume 與 finalization 是否可通過，必須由 `WHD_EXECUTION_RECORD_V2`、atomic control transaction 與 `tools/execution_invocation_exit.py` 的實際 behavior 判定。legacy checkpoint 只作 migration evidence。

## Flow v2 可見進度 / recovery projection — CURRENT

過去曾用 `USER_VISIBLE_CHECKPOINT_GATE`、`CHECKPOINT_RESUME_CONTRACT`、`RUNNING / WAITING_REMOTE / RECOVERING` 等文件 marker 補 user-visible recovery。這些 marker 現在只屬歷史事故語彙，**不得再作 CURRENT execution contract**。

CURRENT 規則：

- durable state 唯一來自 `WHD_EXECUTION_RECORD_V2`；visible progress / CHECKPOINT 只是 observation/projection，不能建立 lease、owner、resume、turn-exit 或 closure authority。
- system/runtime 被切斷後，先 fresh-read ExecutionRecord、generation、lease、structured `next_action`、exact branch/HEAD 與 active_run；無 drift 直接續 exact action。
- `派工`、`執行開發任務`、`monitoring-remote-qa`、`issue-closure-gate` 都是 `FLOW_V2_EXECUTION_BRIDGE_V1` MIRROR，不得互相指定對方為第二套 checkpoint/state owner。
- remote QA exact `active_run/run_id/head_sha` 與 `POLL_QA / ACCEPT_QA / CONSUME_QA / FAIL_QA` 都存在同一 ExecutionRecord；已有可消費 terminal GREEN 時走 `CONSUME_QA` fast path。
- `tests/process/test_checkpoint_resume_contract.py` 與 `tests/process/test_continuous_execution_durable_contract.py` 現在是**反向 anti-regrowth tests**：它們保證 legacy marker 不會被重新塞回 CURRENT/MIRROR entry skills。

> **[FLOW_V2_LEGACY_CHUNK_FENCE_V1]** 下游事故段若仍出現 legacy checkpoint / continuity-controller / WAITING_REMOTE_QA 名稱，只作 historical evidence；CURRENT machine behavior 以 Flow v2 ExecutionRecord + atomic control transaction + invocation-exit machine 為準。

## ISSUE188_EXECUTION_WINDOW_RECOVERY_PITFALL

#188 在 real Tk/Xvfb 與 inherited QA 已 terminal GREEN 後，execution window interruption 發生在 durable writeback 前。如果因視窗重開就把 RED/GREEN/remote QA 全部從頭重跑，會浪費 runner、模糊 tested-head provenance，甚至把新的 harness noise 誤當舊 production regression。

永久規則：

- execution window interruption 只把語意狀態切到 `RECOVERING`；它本身不撤銷既有 completed phase evidence。
- 先 remote refetch production target、反讀 owning Issue recovery checkpoint、核對 work branch + HEAD 與既有 run identity；無 drift 就接 exact next action。
- **只有 drift 才重驗受影響範圍**；不能因 runtime 重開就重跑全部已完成 phase。
- exact tested HEAD / ancestry 未變時，既有 terminal QA 可繼續作 evidence；若 run identity / ancestry 改變才重新分類。
- **使用者不是續跑 scheduler。** recovery identity 驗完且 next action 可自主執行時，要直接續做，不等使用者再說「繼續」。

這些 recovery 提醒不建立第二套 state machine；legacy `RECOVERING` checkpoint 名稱只作事故語彙。CURRENT recovery 由 ExecutionRecord 的 structured next_action / RECONCILE / generation fencing 表達。

## ISSUE188_STALE_WAIT_PITFALL

這次 #188 又暴露另一個長流程失敗模式：checkpoint 寫著 `WAITING_REMOTE_QA`，但實際 GitHub 已無 active run，worker 仍把舊 waiting 字樣當成目前真實狀態，因而無限等待。

永久規則：

- `WAITING_REMOTE_QA` 不是 durable truth；它必須由 exact `run_id + head_sha` 的 live readback 支持。沒有 run identity 或 run 已 terminal，就不得繼續 waiting。
- checkpoint 寫著 WAITING_REMOTE_QA 但 GitHub 已無 active run 時，分類為 `STALE_WAIT`，不是「還在跑」。
- exact run terminal 時立即退出 waiting；非 terminal 但找不到 matching active run 時，以連續 2 次 observation 排除短暫 API 延遲，之後強制進 `RECOVERING_STALE_WAIT`。
- recovery 必須先 remote refetch、反讀 checkpoint、驗 work/production HEAD 與 exact run identity；無 drift 就接 next exact action，不重跑已完成證據。
- global active run = 0 只作 supporting evidence；exact `run_id + head_sha` 才是 canonical remote-QA identity。
- polling cadence 由 `.agents/skills/engineering/monitoring-remote-qa/SKILL.md` bridge 到 Flow v2 active_run 負責，不是使用者責任；durable state / resume / finalization 由 ExecutionRecord + atomic transaction + invocation-exit 負責。**使用者不是 watchdog**，不得靠使用者再輸入「輪／繼續」才讓 stale wait 解鎖。
- `.agents/skills/engineering/monitoring-remote-qa/SKILL.md::STALE_WAIT_WATCHDOG` 與 `tests/process/test_continuous_execution_durable_contract.py` 是 remote-QA/documentation regression guards；它們不取代 executable checkpoint state/finalization authority。

## WORK_ORDER_LINEAGE_PITFALL — HISTORICAL/SUPERSEDED BRANCH MECHANICS

#185 暴露工單級 lineage 缺陷。下方「工單主分支 / 子票 branch」具體 mechanics 已被 Flow v2 generation + canonical root workspace + mutation_scope/root-local-first 取代；只保留『後續工作不得遺失已接受前序成果』這個事故教訓。

永久規則：

- 派工一個含 T1/T2/... 的 Master 工單時，先從當下 authoritative production target 建立唯一 **工單主分支**；此 branch 持有整張工單從第一個 accepted slice 到 final Combined Acceptance 的前序 accepted lineage。
- 子票不得重新從 production target 起跑。下一張子票的 authoritative base 必須是工單主分支目前 accepted HEAD，或是從該 HEAD 開出的短命 `task/QA branch`；完成後回到工單主分支。
- `production target` 在工單完成前只作 **integration target / drift authority**；不能因它尚未包含上一張子票，就拿它覆蓋工單主分支 lineage。
- `task/QA branch` 只負責隔離實作或驗證，不得成為新的長期 lineage owner；驗收後 non-force 回到工單主分支，臨時 QA workflow/branch 依 cleanup 規則處理。
- 工單內所有 checkpoint / owning Issue / handoff 都必須記錄 `work-order branch + accepted HEAD + production target HEAD` 三者，避免只寫 production SHA 造成下一張票誤起跑。
- 只有整張工單 final Combined Acceptance、durable writeback、invariants、cleanup、closing drift audit 全完成後，才把 final verified work-order HEAD **一次 non-force 整合**到 production target。
- 整合後另做 production-head verification/readback；若 FAIL，從 actual production HEAD 開 fresh hotfix/revert branch，不能倒退或 force production。
- 若歷史工單已發生 lineage divergence，先 classify accepted commits，建立/修復單一 work-order lineage，再續工；不得把舊 production branch 當作「比較乾淨」而丟掉前序 accepted lineage。
- `.agents/skills/engineering/派工/SKILL.md::WORK_ORDER_LINEAGE_CONTRACT` 與 `tests/process/test_continuous_execution_durable_contract.py` 是 workflow lineage regression guards；它們不建立另一套 executable continuity state machine。

## REMOTE_TERMINAL_CLOSING_LOCK_GAP — HISTORICAL/SUPERSEDED

### 事故模式

Remote QA 在 `queued / in_progress` 時有 `REMOTE_QA_ACTIVE_LOCK`，所以 30 秒回報後仍會繼續 poll；但 run 一 terminal，remote lock 解除，工作其實通常才進入 counts → invariant → cleanup → tested→closing drift → AI writeback → issue/Master closure。舊流程只有 `assert_finalizable`，沒有 machine-level assistant turn-exit gate，因此最容易在「QA PASS」「code integrated」「process incomplete」回報後結束回合。

### 根因與永久修正

- 根因不是缺少 `NON_TERMINAL_CONTINUE` 文字，而是 enforcement scope 只覆蓋 workflow finalization，沒有覆蓋 assistant turn boundary。
- HISTORICAL fix 曾使用 `tools/continuity_controller.py::assert_turn_exitable`；CURRENT fix 是 `tools/execution_invocation_exit.py::classify_invocation_exit` + durable DONE tuple。
- CURRENT turn-exit 只依 ExecutionRecord state + structured `next_action` + live lease/active_run/closure；terminal-tail `MERGE/FINALIZE` 固定 `CONTINUE_TERMINAL_TAIL`，只有 genuine machine blocker 可中斷。
- Remote terminal 後若還有收尾，必須 `WAITING_REMOTE → RUNNING(next_acceptance_action)`，由 global turn-exit gate 無縫接手 remote lock。
- progress / CHECKPOINT / PASS / integrated / process-incomplete 都只是 observation；只要 machine checkpoint 還有可自主 next action，使用者就不是續跑 scheduler。
- CURRENT behavior authority：`tests/process/test_flow_v2_execution_invocation_exit.py` 與 Flow v2 transaction regressions；legacy continuity-controller tests只作 migration compatibility。

## SILENT_ACTIVE_WORK_PITFALL

### 事故模式

Scheduled Resume 已能自行工作，但 active work 期間完全靜默。對使用者而言，「正常背景執行」「正在等既有 RUN」「Runtime 卡死」外觀完全一樣，導致使用者必須再次輸入「輪／繼續」才能確認系統是不是還活著。

### 永久規則

- active scheduled work 不得用完全靜默作正常 UX；必須 bridge `SCHEDULED_RESUME_PROGRESS_HEARTBEAT`。
- 回報狀態只投影 canonical execution truth：`WORKING / WAITING_REMOTE / RECOVERING / BLOCKED / COMPLETE`，不能建立另一套 state machine。
- WAITING_REMOTE 要帶 exact run identity 與 current step/status；長時間無 remote 變化要明示疑似卡住並進 stale 判定。
- shared lease 被另一 Runtime 合法持有時，要說明 safe no-op，而不是沉默。
- 沒有 active work 才可靜默。
- heartbeat 只是 visibility observation；**進度回報不是停工點**，回報後有自主 next action 就繼續。

CURRENT authority：Flow v2 ExecutionRecord + NON_AUTHORITY runtime observation；`executable-continuity-controller` filesystem bridge 已退休，只保留 alias。

## TERMINAL_EVIDENCE_DELAYED_REPORT_PITFALL

### 事故模式

RUN / task 已經拿到 terminal PASS、FAIL 或 COMPLETE evidence，但執行者繼續做額外 readback、cleanup 或證據整理，直到數分鐘後才回報。對使用者而言，這段空白時間與「卡住」沒有差別。

### 永久規則

- 一旦有 evidence-backed terminal 事實，先**立即回報**，再繼續 secondary verification / cleanup。
- 不得為了讓最終報告更完整而延後已經成立的 PASS / FAIL / COMPLETE 事實。
- immediate report 只是一個 observation；回報後若仍有可自主 next action，仍必須繼續。
- 只有 live terminal evidence 可觸發；不得猜測或提前宣告結果。
- CURRENT authority：terminal fact可立即投影 user-visible progress，但 completion/exit 仍由 Flow v2 durable DONE / invocation-exit machine決定。

## POLLING_WITHOUT_PROGRESS_PRODUCER_PITFALL

### 事故模式

系統反覆輪詢某個狀態，但實際上沒有任何 executor / runner / workflow 在推進。結果看起來一直「有在看」，實際上沒有產生任何進度，最後還要靠使用者再輸入「輪／繼續」。

### 永久規則

- 輪詢只能觀測進度，不能產生進度。
- WAITING_REMOTE 前必須先確認 real progress producer 已存在且 active。
- no producer / no active run / RUN_NOT_CREATED 時，立即停止假等，去執行 prerequisite / trigger / repair。
- terminal producer 立即離開 waiting，接下一個真正執行動作。
- status-only loop 是 continuity regression。
- CURRENT authority：Flow v2 `active_run` + structured `POLL_QA`; observation不能產生進度或 execution authority。

<!-- ISSUE693_COMBINED_ACCEPTANCE_WRITEBACK_V1 -->
## #693 Combined Acceptance durable readback

- domain: `continuous_execution`
- accepted chain: `#687/#688/#689/#690/#691/#692 -> #693`
- integration source head: `64a64d4a0ee8adae81396eaef52c16db97b57d4f`
- retained invariant: Normal stop requires exhaustive blocker/path proof and zero executable leaves; progress reporting is not a stop reason.
- this writeback records durable acceptance/readback only; it does not create a second authority or state machine.
- deployment/readback manifest: `docs/governance/issue693_combined_acceptance_writeback_manifest.json`

<!-- ISSUE702_MUTATING_TOOLCALL_CRASH_RECOVERY_WRITEBACK_V1 -->
## Mutating toolcall crash-recovery canonical invariant

- Mutating work must persist an operation identity before the side effect and recover from durable readback before any ordinary next action after re-entry.
- Canonical crash boundaries are: `prepare → authorize → post-effect → readback → pre-reconcile → post-reconcile`.
- `EFFECT_OBSERVED` means the requested effect is already proven by exact durable/live evidence: **do not replay the mutation**; reconcile the operation and continue from the reconciled state.
- `AMBIGUOUS` means identity/effect cannot be proven: fail closed and repair evidence/authority; never guess whether a mutation happened.
- Canonical CURRENT execution continuity is single-source in Flow v2: durable semantic state=`WHD_EXECUTION_RECORD_V2`; atomic transition=`tools/control_transaction.py`; trusted side-effect/reconcile=`tools/control_transaction_production_executor.py`; invocation exit=`tools/execution_invocation_exit.py`; scheduler projection=`tools/execution_scheduler_view.py`。
- legacy continuity/claim/Claim Activation/Remote Guard runtime 已從 CURRENT tree 移除；歷史 knowledge provenance 不得由 Entry Skill/prompt 重新升格成 competing CURRENT state machine。
- Amendment-wide fault matrix authority is `docs/governance/issue702_crash_fault_injection_matrix.json`; accepted provenance/readback is recorded separately in `docs/governance/issue702_combined_acceptance_writeback_manifest.json`.

## TERMINAL_GREEN_IS_NOT_EXIT_AUTHORITY_V1

CURRENT：QA/CI GREEN 只代表候選驗證成功，不代表 invocation 可以停止。exact-head GREEN 被 ACCEPT_QA / CONSUME_QA 接受且 continuation 進入 MERGE 後，立刻進 no-yield terminal tail；必須連續完成 MERGE → Issue close/readback → FINALIZE → RELEASED/DONE。PR merged 也只是 terminal tail 中段，不是 completion。

防回長規則：不得因「GREEN 已經回報」「PR 已 merge」「本輪已有 substantive transaction」「host boundary 到了」而 YIELD。machine owner=`tools/execution_invocation_exit.py`；terminal tail 固定回 `CONTINUE_TERMINAL_TAIL`。
