looaeedr/whd/個人AI檔案庫/踩坑庫/executable_continuity_controller_pitfall.md

---
whd_doc_role: REFERENCE
whd_contract: continuous-execution-machine
whd_canonical: null
whd_schema: WHD_DOC_META_V1
---
# Executable Continuity Controller / 文件規則不等於執行鎖

> **[HISTORICAL / SUPERSEDED EXECUTION MECHANICS — FLOW_V2_LEGACY_EXECUTION_HISTORY_FENCE_V1]**  
> 本檔保留事故、migration 與舊治理機制做 reference。凡下文出現 `execution claim`、`coord/dispatch-claims`、`execution_claim_guard.py`、Remote Guard、Claim Activation、checkpoint closure、main↔X mirror 等 imperative wording，**都不是 CURRENT 執行指令**。CURRENT authority 固定為 `.agents/skills/engineering/flow-v2-execution/SKILL.md` + native `WHD_EXECUTION_RECORD_V2` + live lease/mutation_scope + atomic control transaction + `STALE_PLAN_MUST_DIE / ONE_ISSUE_ONE_MUTATION_WRITER`。若歷史敘述與 CURRENT contract 衝突，以 Flow v2 為準。

## EXECUTABLE_CONTINUITY_CONTROLLER_PITFALL_V1

### 事故

WHD 已經有 `NONTERMINAL_NEXT_ACTION_GATE`、`REMOTE_QA_ACTIVE_LOCK`、`STALE_WAIT_WATCHDOG`、30 秒 polling、`使用者不是 scheduler` 等完整文字規則，但實際長流程仍會出現「規則說不能停，工作卻在 non-terminal 狀態結束回合」。

根因不是再少一句提醒，而是舊 machine guard 多數只做：讀 Skill / AI Library 文字，再 `assert` 某些 marker 字串存在。這只能證明**文件寫了規則**，不能證明 runtime state 可保存、可恢復，也不能真的拒絕 non-terminal finalization。

### 永久判定
> **[FLOW_V2_LEGACY_CHUNK_FENCE_V1]** 本段以下 legacy imperative 只作歷史 evidence；CURRENT authority 是 `flow-v2-execution` + native `WHD_EXECUTION_RECORD_V2`，不得單獨擷取後升格。

1. **Documentation != enforcement.** `final 禁止`、`使用者不是 scheduler`、`STALE_WAIT_WATCHDOG` 等 marker 只能當文件相容性 guard，不能再被描述為「已鎖死停頓路徑」。
2. 長流程 durable state 的 executable authority 是 `tools/continuity_controller.py`，操作/語意 authority 是 `.agents/skills/engineering/executable-continuity-controller/SKILL.md`。
3. Non-terminal states 固定為 `RUNNING / WAITING_REMOTE / RECOVERING / BLOCKED`，每一個都必須有非空 `next_action`；沒有就 fail closed。
4. `WAITING_REMOTE` 必須有 exact positive `run_id + head_sha`，並在可得時保存 `job_id / log_cursor / evidence`。文字寫著 WAITING 不是遠端真相。
5. checkpoint 必須 versioned + atomic persistence；runtime cut 後 `load_checkpoint → identity/drift verification → exact next_action`，不得重新把使用者當 scheduler，也不得無條件重跑已完成 phase。
6. `assert_finalizable` 是 workflow/issue/acceptance closure 的 machine gate。任何 non-terminal checkpoint 都必須拒絕 finalization；只有 `TERMINAL_SUCCESS / TERMINAL_FAILURE` 可通過 controller gate。
7. Remote run terminal 不等於整張工作 terminal。若 counts / invariants / cleanup / drift / issue closure 還有 next action，state 應回 `RUNNING(next_acceptance_action)`，不得提前落 `TERMINAL_SUCCESS`。
8. `BLOCKED` 代表工作暫時需要外部 authority，但在 controller 層仍是 non-terminal；它不能被拿來繞過 workflow completion gate。
9. 真正驗收必須是 behavior tests：建立 checkpoint、模擬 runtime cut、reload、驗 exact identity/cursor/evidence、嘗試 non-terminal finalization 並確認被拒絕、驗 terminal transition lock。只搜文字不算。
10. 平台仍可能硬切聊天 Runtime；repo controller 無法控制平台。但正確目標是 **platform cut != workflow state loss / remote work stop**：遠端 runner 自己續跑，下一 Runtime 從 durable checkpoint 精準接續。

### 對應 Machine Guard

- `tools/continuity_controller.py`
- `tests/process/test_continuity_controller.py`
- `.agents/skills/engineering/executable-continuity-controller/SKILL.md`
- `.agents/skills/engineering/執行開發任務/SKILL.md::EXECUTABLE_CONTINUITY_CONTROLLER_V1_BRIDGE`
- `.agents/skills/engineering/monitoring-remote-qa/SKILL.md::EXECUTABLE_CONTINUITY_CONTROLLER_V1_BRIDGE`
- `.agents/skills/engineering/issue-closure-gate/SKILL.md::EXECUTABLE_CONTINUITY_CONTROLLER_V1_BRIDGE`

### 禁止說法

- 「Skill 已經寫了，所以不會再停。」——錯，除非 executable state / finalization behavior 有實證。
- 「pytest 有檢查 marker，所以 runtime guard 已完成。」——錯，那只是 documentation contract。
- 「remote run 還在跑，等使用者下次打繼續再查。」——錯；chat runtime 可用時主動 poll，runtime 被硬切後則從 durable run identity 恢復。
- 「平台切掉就沒辦法，所以 checkpoint 沒意義。」——錯；無法控制平台不代表可以接受 state loss 或把 remote scheduler 交給使用者。

## TURN_EXIT_ENFORCEMENT_V2
> **[FLOW_V2_LEGACY_CHUNK_FENCE_V1]** 本段以下 legacy imperative 只作歷史 evidence；CURRENT authority 是 `flow-v2-execution` + native `WHD_EXECUTION_RECORD_V2`，不得單獨擷取後升格。

`assert_finalizable` 只能拒絕「把 non-terminal workflow 宣告完成」，不能單獨拒絕「assistant 在 non-terminal progress 回報後結束目前 turn」。這兩個 boundary 必須分離：

- workflow/issue completion → `assert_finalizable`；
- assistant response/turn boundary → `assert_turn_exitable`。

`RUNNING / WAITING_REMOTE / RECOVERING` 有可自主 next action，因此 turn exit fail closed；`BLOCKED` 代表真正外部 wait，可結束 turn但仍不可 finalizable；terminal states 可通過兩者。特別是 remote run terminal 後，只要 cleanup/drift/closure 未完，必須回 `RUNNING(next_acceptance_action)` 並由 turn-exit guard 接手，不能因 remote lock 解除就回報後停止。

對應 machine guard：`tools/continuity_controller.py` + `tests/process/test_continuity_controller.py`。Skill/AI marker tests 只保護 bridge 存在，不得再次被誤稱為 runtime enforcement。

## MASTER_CHAIN_CHILD_TERMINAL_EXIT_PITFALL_20260921

### 事故

#467/T1 已完成 remote QA、cleanup、drift audit 並 CLOSED/completed，下一張 #468/T2 已 OPEN、exact parent 已寫回、沒有 blocker；assistant 卻把「child terminal」誤當成「整條 Master #464 terminal」，在回報 #467 完成後結束 turn，留下 #468 未 claim。

### 根因

舊 `assert_turn_exitable` 只看單一 checkpoint 的 `RUNNING / WAITING_REMOTE / RECOVERING / BLOCKED / TERMINAL_*`。它不知道 terminal checkpoint 是 leaf/child 還是 Master，因此 `TERMINAL_SUCCESS` 會直接放行 turn exit，無法表示「這張 child 完成，但 Master 還有可自主執行的 next child」。

### 永久硬閘門
> **[FLOW_V2_LEGACY_CHUNK_FENCE_V1]** 本段以下 legacy imperative 只作歷史 evidence；CURRENT authority 是 `flow-v2-execution` + native `WHD_EXECUTION_RECORD_V2`，不得單獨擷取後升格。

- Canonical executable owner：`tools/continuity_controller.py`。
- terminal child 若屬 Master/work-order chain，checkpoint 必須結構化保存 `master_issue + chain_state + next_issue + chain_next_action/chain_reason`。
- `NEXT_CHILD_EXECUTABLE`：child 可關，但 turn exit **必須拒絕**；scheduled resume / CLI resume 皆回 exact `chain_next_action`。
- `NEXT_CHILD_BLOCKED`：只允許 genuine external authority/capability wait，且需 reason。
- `CHAIN_COMPLETE`：只有整條 Master 已真正 terminal。
- `USER_STOPPED`：只有使用者明確停止／取消 chain。
- 外層已知 Master 時必須傳 `expected_master_issue`；checkpoint 漏填或填錯 Master handoff 一律 fail closed。
- 不得從聊天文字、Issue comment、commit message 或 evidence 字串推理 handoff authority。

Primary regression：`tests/process/test_issue473_master_chain_turn_exit_gate.py`。判斷式固定為：

`run terminal != child terminal != Master-chain terminal`

## TERMINAL_CLOSURE_HALF_STATE_PITFALL_V1

### 症狀
- child checkpoint 已 `TERMINAL_SUCCESS`，但 owning Issue 還 open、claim 還在 `RECOVERING/CLOSING`；
- 或 Issue/PR 已 close/merge，但 shared claim 還 active、next_action 還停在舊的 pre-merge 動作；
- scheduler 把「terminal checkpoint」誤當成「整個 process 可以停」。

### 根因
acceptance terminal 與 process closure 被拆成不同 transaction，但舊 `assert_turn_exitable` 只看 continuity state / Master handoff，沒有 machine-readable closure lifecycle。

### 永久防線
> **[FLOW_V2_LEGACY_CHUNK_FENCE_V1]** 本段以下 legacy imperative 只作歷史 evidence；CURRENT authority 是 `flow-v2-execution` + native `WHD_EXECUTION_RECORD_V2`，不得單獨擷取後升格。
`tools/continuity_controller.py` 的 canonical closure progression 是：

```text
FINALIZATION_PENDING
→ ISSUE_CLOSE_PENDING
→ RELEASE_HANDOFF_PENDING
→ CLOSED
```

terminal 但 `closure_state != CLOSED` 一律拒絕 turn exit，並由 `closure_next_action` 繼續。舊 terminal JSON 缺 closure metadata 時 fail-safe 回復成 `FINALIZATION_PENDING`。

最後一步不可「先 claim RELEASED，再補 checkpoint CLOSED」，因 release 後已失去 active owner。必須在**同一個 coordination closure commit**原子寫入：

1. checkpoint `closure_state=CLOSED`；
2. shared claim `phase=RELEASED`；
3. successor / Master chain handoff。

即使 child CLOSED，`NEXT_CHILD_EXECUTABLE` 仍由 Master chain gate 阻擋 turn exit並直接續下一票。

## ISSUE633_FINALIZATION_PROOF_ORDER_PITFALL> **[FLOW_V2_LEGACY_CHUNK_FENCE_V1]** 本段以下 legacy imperative 只作歷史 evidence；CURRENT authority 是 `flow-v2-execution` + native `WHD_EXECUTION_RECORD_V2`，不得單獨擷取後升格。
 — proof 前先進 ISSUE_CLOSE_PENDING

2026-09-25 在 #632 整合後 fresh-read closure contract 發現：若流程採「`FINALIZATION_PENDING` 先 authorize/verify proof → 再把 checkpoint 改成 `ISSUE_CLOSE_PENDING` → close Issue」，第二步會改變 checkpoint fingerprint，導致剛取得的 proof 在真正 close 前立即 stale。

永久順序只有一個：

```text
FINALIZATION_PENDING
→ durable advance to ISSUE_CLOSE_PENDING
→ authorize-finalization + verify-finalization-proof on exact current checkpoint
→ NO CHECKPOINT MUTATION
→ close owning Issue
→ fresh readback closed/completed
→ advance RELEASE_HANDOFF_PENDING
→ atomic CLOSED + RELEASED + successor handoff
```

Machine 防線：`tools/continuity_controller.py::authorize_finalization` 必須拒絕任何 `closure_state != ISSUE_CLOSE_PENDING`。proof 產生後若 checkpoint evidence、closure state 或任何 serialized field 被改動，舊 proof 一律 stale；不得用舊 proof 關單。

## ACTIVE_DELEGATED_WORK_FALSE_STALE_PITFALL_V1> **[FLOW_V2_LEGACY_CHUNK_FENCE_V1]** 本段以下 legacy imperative 只作歷史 evidence；CURRENT authority 是 `flow-v2-execution` + native `WHD_EXECUTION_RECORD_V2`，不得單獨擷取後升格。

#631 → #636 證明 parent 可安靜但 delegated helper 仍在合法工作。

1. stale evaluator 先解析 parent structured delegated pointers。
2. open + active child = `ACTIVE_DELEGATED_WORK`、non-actionable；沿鏈到 child leaf。
3. child stale 才接 child；不得 takeover parent 再開 helper。
4. parent 宣告 child但 evidence missing/malformed → fail closed。
5. 同 `parent_issue + helper_key` 只能一個 active helper，已有就 resume/reuse。
6. child terminal = Issue closed + claim terminal/released；half-terminal 先 reconciliation。

Canonical machine owner：`tools/stale_claim_takeover.py`。

## EQUIVALENT_DUPLICATE_GREEN_PITFALL_V1> **[FLOW_V2_LEGACY_CHUNK_FENCE_V1]** 本段以下 legacy imperative 只作歷史 evidence；CURRENT authority 是 `flow-v2-execution` + native `WHD_EXECUTION_RECORD_V2`，不得單獨擷取後升格。

2026-09-25 #648 收尾時，同一個 `pr-write` mutation identity 被重複送出 Remote Guard，產生兩張仍有效且完全等價的 GREEN（runs `36095688419` / `36095692365`）。舊 classifier 只要看到兩張 matching GREEN 就一律 `AMBIGUOUS → FAIL_CLOSED`，導致合法收尾只能等 TTL 全數過期。

永久規則：

1. 只有 **mutation-relevant identity 完全相同**的 GREEN 才能折成 equivalent group；identity 包含 issue / worker / executor / action / branch / base / head / claim blob / guard authority / tested target / changed files，以及 takeover 專屬 identity。
2. equivalent group 沒有 durable mutation readback、且仍有 live member 時，整組只代表**一個** `PENDING` mutation。
3. 可 consume 的 canonical receipt 固定取「仍有效成員中 `issued_at` 最早者；同時則 `run_id` 最小者」。已過期 member 不得因另一張 duplicate 還活著而重新取得 mutation authority。
4. shadow receipt 永遠不可獨立 consume；請求 shadow `run_id` 必須 identity-mismatch fail closed。
5. 任一 equivalent member 的 action-specific durable readback 若證明 mutation 已發生，整組一起折成 `CONSUMED` 或 `MUTATION_DONE_RECONCILE_ONLY`，避免 shadow replay。
6. 全組皆 expired 才是 `EXPIRED_UNCONSUMED`；TTL 語意不因 dedupe 改變。
7. 只要任一 mutation-relevant identity 不同，仍維持真正的 `AMBIGUOUS → FAIL_CLOSED`，不得用 dedupe 掩蓋衝突。

Canonical machine owner：`tools/execution_claim_guard.py`。Primary regression：`tests/process/test_issue643_guard_transaction_gate.py`。#651 focused acceptance：run `36097453177`，23 passed / 0 failed。

<!-- ISSUE646_PITFALL_WRITEBACK_V1 -->
## #641 fingerprint normalization pitfall

#641 first finalization run 36051135751 因 raw JSON fingerprint 與 canonical Checkpoint normalization 不一致而 FAIL；改走 load_checkpoint + checkpoint_fingerprint 後 run 36051265277 GREEN。永久禁止自行 hash raw checkpoint JSON。

## EXPIRED_UNCONSUMED recovery pitfall
GREEN 過期且沒有 durable mutation proof時，舊 receipt 永久不可 consume。正確恢復：fresh exact identity → EXPIRED_UNCONSUMED → mint fresh recovery Guard。不得因『以前 GREEN』直接 mutation。

## Interactive liveness / provenance gap
#646 暴露 scheduler 有 heartbeat、chatgpt_interactive 沒有對稱 runtime liveness，且 generic executor_source 無法指出哪個聊天室。Required follow-up：interactive heartbeat；conversation/chat identity + invocation identity；scheduler lane + invocation identity；heartbeat不得取代 ownership authority。

## 2026-09-26 — legacy post-commit receipt-window drift

症狀：historical work commit 已存在、claim/checkpoint 尚停在 H0；H1 又確實是 H0 direct child、changed files 也與 prior GREEN Guard 完全一致，但 commit timestamp 晚於該 receipt 的 `expires_at`。ordinary post-commit reconciliation 會正確 FAIL，不能因「看起來就是那顆 commit」直接補 claim HEAD。

修復規則：只走 `LEGACY_POSTCOMMIT_RECONCILIATION_REPAIR_V1`。owner-authored `WHD_LEGACY_POSTCOMMIT_RECONCILE_V1` 必須 exact 綁 current claim blob、H0/H1、prior Guard run/request 與 actual changed files；trusted Remote Guard 再 fresh-read GitHub durable evidence。只允許 direct-child、唯一 expired matching receipt，且只做 claim/checkpoint HEAD reconciliation。任何 identity drift、merge/multi-hop、extra file 或 multiple candidate 都 fail closed。此 escape hatch 不得取代 normal receipt-window discipline。

## EXECUTION_INTENT_SCOPE_EXPANSION_PITFALL_V1

### 事故

Continuity 的「non-terminal 不能停」與 Master chain 的「NEXT_CHILD_EXECUTABLE 要續做」若缺少 execution-intent boundary，會把正確的持續執行規則錯用到 `UPDATE_ONLY` 或單票 `EXECUTE_TICKET`：

- 更新一條規則後因 repo 還有 open Issue 而自動開始施工；
- 單票 closure 完成後只因 dependency graph 有 successor 就自動 claim 下一張；
- recovery capability 被當成每張票固定 lifecycle phase。

### 永久規則

- Continuity 只能延續已授權 execution mode，不能創造 execution authority。
- `UPDATE_ONLY` 不進 continuity execution state machine。
- `EXECUTE_TICKET` 只 resume / close 當前 ticket，不因 successor 可見而擴張 scope。
- 只有 `EXECUTE_CHAIN` / `SCHEDULER_LANE` 才能把 `NEXT_CHILD_EXECUTABLE` 當成跨 ticket continuation authority。
- `ISSUE_EXISTENCE_IS_NOT_EXECUTION_AUTHORITY`：open/unblocked Issue、空工作槽、next_action、Guard availability 皆不足以啟動新 scope。
- `RECOVERY_IS_EXCEPTION_NOT_PHASE`：`RECOVERING` 只在 fresh machine evidence 證明 failure/drift/interruption 後存在；修復後立即回 `RUNNING` normal path。
- 這些規則不放寬 claim/Guard/finalization safety；它們只限制 scope expansion 與 recovery routing。

## MALFORMED_TERMINAL_CHECKPOINT_REPAIR_PITFALL_V1

### 事故

#733 在 code/parity 已完成後，terminal checkpoint 被寫成不存在的 `closure_state=READY_FOR_FINALIZATION`。結果三條既有路全部正確 fail closed：

- Remote Finalization 無法 parse checkpoint；
- ordinary Remote Guard 回 `ACTIVE_CLAIM_REQUIRES_CHECKPOINT`；
- Claim Activation `reactivate` 拒絕 active claim 搭 terminal checkpoint。

### 永久規則

這種狀態不能手改 `coord/dispatch-claims`、不能把 terminal checkpoint 降回 RUNNING、不能先把 claim RELEASED，也不能擴大 ordinary `reactivate`。

唯一 recovery：
`repair_malformed_terminal_checkpoint` 先對 raw prior payload做窄 canonical normalization，trusted Claim Activation `terminal-checkpoint-repair` 再用 exact prior claim/checkpoint blob + coord parent CAS 原子換成 candidate pair。

Candidate claim 必須完全不變；candidate checkpoint 只允許保留同一 issue/branch/head/`TERMINAL_SUCCESS`，把 malformed closure lifecycle 正規化成 `FINALIZATION_PENDING`。任何其他 drift 或已合法 closure state 一律拒絕。Repair 之後仍必須重新走 Remote Finalization → Issue close/readback → atomic CLOSED + RELEASED。

## 2026-09-27 — 中途回報被誤當停止點 / BLOCKED proof 不夠 fresh-unique

### 事故

#687 已把 bare `BLOCKED` 升級成需要 `exhaustive + executable_leaf_count=0` 的 machine proof，但仍留下三個可重複風險：

- evidence 字串可以自稱「fresh」，沒有 machine timestamp freshness；
- blocker 沒有 canonical identity/count，無法證明真的是**唯一** blocker；
- blocker proof 只作 caller 參數，沒有持久化在 owning checkpoint；trusted/live gate 也容易把 genuine BLOCKED 與 terminal closure 混成同一路徑。

這會讓「我已回報進度／我現在 BLOCKED」有機會被錯解成自然 turn boundary，或反過來讓 genuine external blocker 被 terminal close/release contract 卡住。

### 永久修正

`TURN_EXIT_TERMINAL_OR_FRESH_UNIQUE_BLOCKER_HARD_GATE_V1`：

1. **中途回報永遠不是停止權限**。progress/status/CHECKPOINT/Guard result/partial QA 都只是 observation。
2. 正常 return 只有兩條：真正 terminal closure，或 canonical fresh unique BLOCKED proof。
3. BLOCKED proof 必須 durable 寫入 owning checkpoint，並由 `tools/continuity_controller.py` 驗：
   - `exhaustive=true`；
   - `executable_leaf_count=0`；
   - `blocker_count=1`；
   - canonical `blocker_id` 類別與 stop reason 一致；
   - timezone-aware `observed_at`，max age 300 秒、future skew 30 秒。
4. progress/checkpoint/status 觀測 identity 不得冒充 blocker；proof stale、多 blocker、仍有 executable leaf一律 RED。
5. genuine BLOCKED 是 non-terminal：Issue 保持 open、claim 保持 active；不可用 BLOCKED 順便 close/release。
6. active remote run / delegated executable work 存在時，即使 blocker proof 其他欄位都對，也不得 turn-exit。
7. proof 過期必須 fresh-read external durable state 並更新 checkpoint；禁止 replay 舊 evidence。
8. hard gate RED 且仍有合法自主 path時，同一 turn 立即繼續，不得先回報後 return。

Primary machine regression：`tests/process/test_issue787_turn_exit_blocker_authority.py`、`tests/process/test_issue644_trusted_turn_exit_gate.py`。文件只 bridge；唯一 runtime evaluator 仍是 `tools/continuity_controller.py`。

<!-- ISSUE693_COMBINED_ACCEPTANCE_WRITEBACK_V1 -->
## #693 Combined Acceptance durable readback

- domain: `continuity_controller`
- accepted chain: `#687/#688/#689/#690/#691/#692 -> #693`
- integration source head: `64a64d4a0ee8adae81396eaef52c16db97b57d4f`
- retained invariant: Checkpoint/next_action continuity stays machine-owned; terminal closure requires verified finalization and atomic CLOSED+RELEASED.
- this writeback records durable acceptance/readback only; it does not create a second authority or state machine.
- deployment/readback manifest: `docs/governance/issue693_combined_acceptance_writeback_manifest.json`

## 2026-09-26 — local Guard stdout GREEN 不等於 durable post-commit authority

症狀：runtime 本機執行 `tools/execution_claim_guard.py` 得到 `EXECUTION_CLAIM_GUARD_GREEN` 後完成 commit，但 shared claim 仍停在 H0；既有 reconciler 只會消耗 Remote Guard request/receipt，因此 H1 雖合法卻無 durable receipt 可被 machine 反讀。

永久修正：local Guard mutation 若會讓 branch H0→H1，必須把結果持久化成 owning Issue 上唯一的 owner-authored `WHD_LOCAL_GUARD_RECONCILE_V1`，exact 綁 issue/worker/source/branch/base/current claim blob/H0/H1/actual changed files；reconciler 透過 `--local-guard-proof` fresh-read 驗證。local proof 僅允許單一 direct-child H1，duplicate/malformed/foreign/mismatched proof 一律 fail closed。若無法 durable 化 local GREEN，該 mutation 改走 Remote Guard，禁止再留下只有 stdout 的 Guard authority。

## TERMINAL_SCHEDULER_NO_CENSUS_FALSE_EXIT_PITFALL_V1

### 事故
scheduler child 已 `TERMINAL_SUCCESS / CLOSED / RELEASED` 時，舊 canonical turn-exit 只驗 child closure、claim release、active run/delegated work；因此即使 lane 還有 scheduler-authorized ready leaf，也可能先產生 `TURN_EXIT_PERMITTED`，再由 scheduler END 合法收工。若 `READY_WORK_CENSUS_V1` 只存在 prompt/Skill，仍只是 documentation，不是 executable stop gate。

### 永久防線
> **[FLOW_V2_LEGACY_CHUNK_FENCE_V1]** 本段以下 legacy imperative 只作歷史 evidence；CURRENT authority 是 `flow-v2-execution` + native `WHD_EXECUTION_RECORD_V2`，不得單獨擷取後升格。
- scheduler lane normal exit 另需 machine-readable `READY_WORK_CENSUS_V1` proof。
- proof exact 綁 lane、invocation、claim/checkpoint blobs、checkpoint fingerprint 與本次 turn-exit request identity；舊 proof / replay / durable observation drift 一律 fail closed。
- `MUST_CLAIM` 或 `executable_leaf_count > 0` 固定 `EXECUTABLE_LEAF_EXISTS` 並暴露 exact continuation；不能先 END 再等下一 wake。
- zero-leaf 只有在 `exhaustive=true` 且每個 candidate 都有 fresh durable exclusion evidence + canonical exclusion classification 時可通過。
- turn-exit receipt 必須帶 census fingerprint，scheduler END 必須 exact 綁同一 fingerprint，避免 pre-census permit 被重播。
- #764 保持 producer/prompt SSoT；#769 consumer gate 不建立第二套 discovery authority。

Primary owner：`tools/continuity_controller.py`；trusted transport：`.github/workflows/whd-turn-exit-gate.yml`；regression：`tests/process/test_issue769_terminal_scheduler_census_exit_gate.py`。

<!-- ISSUE702_MUTATING_TOOLCALL_CRASH_RECOVERY_WRITEBACK_V1 -->
## Mutating toolcall crash-recovery canonical invariant> **[FLOW_V2_LEGACY_CHUNK_FENCE_V1]** 本段以下 legacy imperative 只作歷史 evidence；CURRENT authority 是 `flow-v2-execution` + native `WHD_EXECUTION_RECORD_V2`，不得單獨擷取後升格。

- Mutating work must persist an operation identity before the side effect and recover from durable readback before any ordinary next action after re-entry.
- Canonical crash boundaries are: `prepare → authorize → post-effect → readback → pre-reconcile → post-reconcile`.
- `EFFECT_OBSERVED` means the requested effect is already proven by exact durable/live evidence: **do not replay the mutation**; reconcile the operation and continue from the reconciled state.
- `AMBIGUOUS` means identity/effect cannot be proven: fail closed and repair evidence/authority; never guess whether a mutation happened.
- Canonical semantic owners remain single-source: generic operation continuity = `tools/continuity_controller.py`; Guard transaction semantics = `tools/execution_claim_guard.py`; scheduler host-state identity/readback = `tools/scheduler_state_reconciliation.py`; Claim Activation readback = `tools/claim_activation_recovery.py`.
- Entry Skills/prompts route into those owners; they must not implement competing continuity, Guard, scheduler-state, or claim-activation state machines.
- Amendment-wide fault matrix authority is `docs/governance/issue702_crash_fault_injection_matrix.json`; accepted provenance/readback is recorded separately in `docs/governance/issue702_combined_acceptance_writeback_manifest.json`.
