looaeedr/whd/docs/superpowers/checkpoints/issue335-t2-green-candidate.md

# #335 T2 GREEN candidate

- Production base: `4bdb0e0366b3accb983a25365cc7b29008a74544`
- RED RUN: `35337570184`
- Minimal implementation: `3778e2c6c60352cb751ba78daf3f418d08ff376f`
- Output controls moved to `top_command_row` as a plain Frame.
- 3D display controls moved above global settings and use a plain Frame.
- Existing DXF/STOCK/export-selection callback and state owners are unchanged.
