looaeedr/whd/docs/superpowers/checkpoints/issue336-t3-green-candidate.md

# #336 T3 GREEN candidate

- Production base: `6f3dc763ac22a1f56a1fa80f817ae574ba0706a5`
- Exact RED RUN: `35338152926`
- Minimal implementation: `88077f5366bc990974f0e3beb10f4a791ee429dd`
- Sheet-metal menu now contains real parts only.
- Fixed three-way content switch: 輸入區 / 組合體 / 截角資料.
- Switch has no independent mode variable; it projects existing `_phase6_3d_display_mode`.
- DM7 / `designer_workspace.active_part` / Structure Tree physical identities remain authoritative.
