looaeedr/whd/docs/superpowers/checkpoints/issue337-t4-final-candidate.md

# #337 T4 final candidate

- Production base: `43c701b08ae802789db4b501475697b0f2b966d7`
- Exact RED: `35338901019`
- Shared role implementation: `733435a0bd6c3978e66511181aecbbf7220fbfab`
- Source-contract robustness fixes: `1127475cc662e27a0b8bfa05f7983d1807b3a098`, `faa663712b385dd385210cdc433ecbbcc6483459`
- Runtime effective-style probes remain the acceptance authority.
