looaeedr/whd/docs/superpowers/checkpoints/issue451-t9-preflight-evidence.md

---
whd_doc_role: REFERENCE
whd_contract: issue451-t9-preflight-evidence
whd_canonical: null
whd_schema: WHD_DOC_META_V1
---

# #451 T9 Preflight / Execution Evidence

## Identity
- MASTER_ID: 441
- TASK_ID: T9
- OWNING_ISSUE: #451
- WORK_BRANCH: `refactor/issue451-t9-durable-writeback-20260921`
- EXPECTED_PARENT_SHA: `4b401077d457acd1e754366637c595b3d82f38d4`
- TARGET_X: `cleanup/2d-3d-sync`
- FROZEN_X_BASE_SHA: `2b9aeccee2c91446ca02cbfe9fdcefee587ba29e`
- CURRENT_X_HEAD_OBSERVATION: `86c6b1aaa391c596dc9ff85b0fd9b34b1c3fba57`
- ROLE: T9 Implementer

## Planned changed files
- `個人AI檔案庫/第二層_專案與SOP/12_WHD_FoldDesignerBridgeOwnership規則.md`
- `個人AI檔案庫/第二層_專案與SOP/09_WHD_Canonical_Authority_Map.md`
- `docs/superpowers/checkpoints/issue451-t9-preflight-evidence.md`
- remove `.github/workflows/qa-issue442-t0-census.yml`
- remove `.github/workflows/qa-issue443-t1-dead-glue.yml`

## Required Skills read
- 派工
- issue-closure-gate
- executable-continuity-controller
- monitoring-remote-qa
- long-log-context-safe-execution

## Required references read
READ_REFERENCE: 個人AI檔案庫/第二層_專案與SOP/06_踩坑記錄與防錯經驗庫.md
READ_REFERENCE: 個人AI檔案庫/第二層_專案與SOP/07_WHD技能發現與掃描深模組規則.md
READ_REFERENCE: 個人AI檔案庫/第二層_專案與SOP/08_WHD技能建立與修改規則.md
READ_REFERENCE: 個人AI檔案庫/第二層_專案與SOP/09_WHD_Canonical_Authority_Map.md
READ_REFERENCE: 個人AI檔案庫/第二層_專案與SOP/09_X第二主分支與獨立工單鏈治理規格.md
READ_REFERENCE: 個人AI檔案庫/第二層_專案與SOP/11_WHD組合體SharedContent呈現規則.md
READ_REFERENCE: 個人AI檔案庫/踩坑庫/issue_closure_completion_pitfalls.md
READ_REFERENCE: 個人AI檔案庫/踩坑庫/executable_continuity_controller_pitfall.md
READ_REFERENCE: 個人AI檔案庫/踩坑庫/long_log_context_safe_execution.md

## Accepted predecessor decisions reread
- #444 / T2: `BENDING_UI_OWNER=phase6_bending_ui.py`; bridge keeps only compatibility transaction delegate/temporary monkey-patch seam.
- #445 / T3: deepen existing `phase6_settings_panel.py`; no competing Settings owner.
- #446 / T4: `phase6_registry_diagnostics_panel.py` owns Registry diagnostics presentation; controller/domain retains rule/promote/manufacturing semantics.
- #447 / T5: `NO_EXTRACTION`; no `phase6_workspace_shell.py`; one shared content surface remains.
- #448 / T6: `C_KEEP_BRIDGE_COMPATIBILITY`; no shallow Part Editor session extraction.
- #449 / T7: `_fix11_init` is bootstrap-only lifecycle/composition root.
- #450 / T8: RUN `35590479636` GREEN; R1-R9 all satisfied; accepted cleaned predecessor `4b401077d457acd1e754366637c595b3d82f38d4`.

## Integration drift census
- frozen X → sealed chain: ahead 94 / behind 0
- frozen X → current X: ahead 36 / behind 0
- current X ↔ sealed chain: diverged; merge-base remains frozen X `2b9aecce...`
- therefore T9 must not fast-forward or rebase the sealed chain onto current X.
- integration must be a fresh non-force integration step after durable writeback and cleanup.

## Boundaries
- validation evidence remains validation/provenance only; it does not become mechanical/manufacturing truth.
- no force push.
- no direct write to `cleanup/2d-3d-sync` before integration acceptance.
- one-shot QA residue must be zero before final integration.
- post-integration smoke and exact production SHA readback are mandatory.

## Next exact action
Write the durable Fold Designer Bridge ownership CURRENT document, update the Canonical Authority Map, remove the two remaining one-shot QA workflows, then run branch-local authority/ownership/protected-file validation before integration.
