looaeedr/whd/docs/superpowers/checkpoints/issue522-a1-dead-glue-census.md

---
whd_doc_role: REFERENCE
whd_contract: issue522-a1-dead-glue-census
whd_canonical: null
whd_schema: WHD_DOC_META_V1
---

# Issue #522 / Phase 6 A1 — Exhaustive Dead-Glue Evidence

- Master: #520
- Issue: #522
- Accepted parent HEAD: `23fd989edfa35583af8e3435ca86fc08835e4260`
- Census RUN: `35761530082`
- Census HEAD: `1fbf1ac691d6e476f673d0db1249045c2b047c4e`
- Artifact ID: `10710820254`
- Artifact SHA/result source: GitHub Actions exact-branch tracked-tree census
- Production deletion authorized by evidence: **none**
- Production behavior change: **0**

## Decision

The exhaustive scan covered all **327** A0 `BOUNDARY_RECONSIDERATION_CANDIDATE` symbols against all tracked text files. Every candidate has at least one runtime/test/runtime-text reference after excluding its own definition.

Therefore:

```text
DEAD_CANDIDATE_COUNT=0
LIVE_CANDIDATE_COUNT=327
MALFORMED_DEFINITION_COUNT=0
A1_PRODUCTION_DELETION_COUNT=0
```

A1 must not delete code to manufacture LOC reduction. Unresolved ownership/reduction proceeds through A2/A3 and, if MRG remains RED, mandatory Stage B.

## Raw census summary

The requested file reference is not currently visible. Use files.search or files.list to rediscover the file, then retry with a returned ref_id or file_id.
