looaeedr/whd/bug.txt

3D有的顯示資訊2D也要有
中隔的預設尺寸錯了 2D沒有顯示中隔也沒有框 3D中隔操作時會亂跳 受電箱封頭尾的基準孔錯了 底板下縮 文字大小中時 看不見 封頭尾 上 下 左 右的選擇框可以在窄一點 3D變2D也要跟著變啊 受電箱的中隔還有框都不見了 先查原因啊
中隔是 W-2T 成形高要看箱身是什麼種類
