looaeedr/whd/修改日誌/20260906.md

### [04:46:00] 變更紀錄
- **變更檔案**：`.gitignore`
- **Git 備份點**：`backup-20260906-044107`
- **Git Commit**：`058bbad`
- **修改摘要**：執行第一階段安全快取與暫存檔清理，清理全專案 `__pycache__`、`.pytest_cache`、`*.pyc` 與 `logs/` 內殘留之 `*.lock` 檔案，並將 `.pytest_cache/` 與 `*.lock` 補入 `.gitignore` 避免後續重複污染 Git 狀態。

### [05:04:00] 變更紀錄
- **變更檔案**：`ae_engine/assembly_placement.py`, `docs/superpowers/checkpoints/dispatch/T1.state.md`, `docs/superpowers/checkpoints/dispatch/T1.journal.jsonl`
- **Git 備份點**：`backup-20260906-050245`
- **Git Commit**：`268e6bc`
- **修改摘要**：完成 T1 工單；修復 `ae_engine/assembly_placement.py` 中隔定位演算法，支援 `C0_R0|R1` 與 `C0:R0|R1` 水平邊界正則相容、拓撲錯誤訊息斷言與 Y 軸從頂邊起算的正確偏移量，`test_assembly_placement_contract.py` 與 `test_assembly_placement_divider.py` 6 項單元測試全數通過。

### [05:36:00] 變更紀錄
- **變更檔案**：`ae_engine/assembly_geometry.py`, `ae_engine/assembly_placement.py`, `ae_engine/door_dividers.py`, `fold_designer_bridge.py`, `gui.py`, `tests/test_assembly_placement_contract.py`, `tests/test_assembly_placement_divider.py`, `tests/test_phase6_t05_box_body_dividers.py`, `docs/superpowers/checkpoints/dispatch/T2.journal.jsonl`, `docs/superpowers/checkpoints/dispatch/T2.provenance.md`, `docs/superpowers/checkpoints/dispatch/T2.state.md`, `logs/preflight/20260906_t2_implementation_evidence.txt`
- **Git 備份點**：`backup-20260906-052530`
- **Git Commit**：`303a671`
- **修改摘要**：完成 T2 工單；實作 2D/3D 共用 Divider 與 Inner Door Projection。水平中隔遇外側邊界正確扣除板厚 (W-2T)、水平中隔 X 座標依據所屬欄位居中對齊；補齊 3D Assembly 空間方位映射與單向缺失之 mesh profile；於 2D Door Layout 總覽畫布即時渲染實體中隔與內門框；更新單元測試並建立 T2 派工檢查點與 journal。

### [05:47:00] 變更紀錄
- **變更檔案**：`phase6_designer_workspace.py`, `phase6_workspace_controller.py`, `fold_designer_bridge.py`, `gui.py`, `tests/test_phase6_workspace_controller.py`, `tests/test_phase6_workspace_projection.py`, `docs/superpowers/checkpoints/dispatch/T3.journal.jsonl`, `docs/superpowers/checkpoints/dispatch/T3.provenance.md`, `docs/superpowers/checkpoints/dispatch/T3.state.md`, `logs/preflight/20260906_t3_workspace_snapshot_evidence.md`
- **Git 備份點**：`backup-20260906-054000`
- **Git Commit**：`08449ec`
- **修改摘要**：完成 T3 工單；實作 3D Confirm 完整權威工作區快照（Authoritative Workspace Snapshot）。解耦 `phase6_designer_workspace.py` 對 `ae_engine` 之直接依賴以修復架構違規；於 `Phase6WorkspaceController` 擴充支援 `part_features`、`part_face_features` 與 `assembly_placements` 之保存與快照導出；在 Bridge `_phase6_collect_workspace_state` 與 3D Confirm payload 補齊完整裝配幾何與配置契約；更新 `gui.py` 存儲邏輯並新增無損往返單元測試。

### [06:28:00] 變更紀錄
- **變更檔案**：gui.py, phase6_designer_workspace.py, 
old_designer_bridge.py, 	ests/test_phase6_2d_3d_round_trip.py, docs/superpowers/checkpoints/dispatch/T4.state.md, docs/superpowers/checkpoints/dispatch/T4.journal.jsonl, docs/superpowers/checkpoints/dispatch/T4.provenance.md, docs/superpowers/checkpoints/T4-checkpoint-20260906.zip
- **Git 備份點**：ackup-20260906-062600
- **Git Commit**：22d3b97
- **修改摘要**：完成 T4 工單；實作 2D Apply 與 2D->3D->2D 往返一致性（Round-trip Integrity）。於 gui.py 擴充 _apply_fold_designer_live_snapshot 支援 3D Confirm payload 完整寫回 2D 權威狀態（含孔特徵、中隔/門版型配置、內門與裝配定位）；在 phase6_designer_workspace.py 補齊工作區子節點裝配定位保留邏輯；於 
old_designer_bridge.py 實現裝配定位冪等查詢防漂移；新增 	ests/test_phase6_2d_3d_round_trip.py 7 項單元測試並全數 PASS，全套 52 項裝配與工作區整合測試無回歸；打包實體 T4 Checkpoint ZIP 並更新派工記錄。

### [06:34:00] 變更紀錄
- **變更檔案**：docs/superpowers/specs/2026-09-06-endcap-hole-provenance-trace.md, 	ests/test_phase6_t05_endcap_hole_provenance_contract.py, docs/superpowers/checkpoints/dispatch/T5.state.md, docs/superpowers/checkpoints/dispatch/T5.journal.jsonl, docs/superpowers/checkpoints/dispatch/T5.provenance.md, docs/superpowers/checkpoints/T5-checkpoint-20260906.zip
- **Git 備份點**： ackup-20260906-063200
- **Git Commit**：84e2e2c
- **修改摘要**：完成 T5 工單；執行封頭／封尾 Hole & Secondary Feature 完整程式碼與幾何追溯。產出 docs/superpowers/specs/2026-09-06-endcap-hole-provenance-trace.md 規格書，包含完整 Provenance Table 與 4 項固定特徵（左右吊掛孔、方孔、封尾底部中心圓孔）及 1 項自訂特徵之 9 大製造與幾何解答；確立 Vault 固定孔位在 Receiving 封頭尾為 DO_NOT_SHARE 邊界防護；撰寫 	ests/test_phase6_t05_endcap_hole_provenance_contract.py 4 項單元測試全數 PASS，全套 56 項相關整合測試無回歸；產出實體 T5 Checkpoint ZIP 並更新派工記錄。

### [06:54:00] 變更紀錄
- **變更檔案**：`ae_engine/ae.py`, `ae_engine/manufacturing_api.py`, `ae_engine/sheetmetal_features.py`, `tests/test_ae_geometry_integration.py`, `tests/test_phase6_t05_endcap_hole_provenance_contract.py`, `logs/preflight/20260906_t6_receiving_hole_policy_evidence.md`
- **Git 備份點**：`backup-20260906-064611`
- **Git Commit**：`df90ef3`
- **修改摘要**：完成 T6 工單；實作 Receiving 封頭／封尾固定特徵隔離策略（Receiving EndCap Fixed Feature Policy Isolation）。依 T5 追溯規格書，建立 `ReceivingEndCapFeaturePolicy` 與 `resolve_receiving_endcap_fixed_features`，並以 `resolve_endcap_fixed_features_for_model` 集中由 `model_name` 或明確策略進行路由，預設關閉 Vault 特徵避免破孔錯位；於 `ae.py` 與 `manufacturing_api.py` 串接 `model_name` 傳遞；更新 `test_ae_geometry_integration.py` AST 防護測試；修正 T5 測試檔 UTF-8 BOM；全套相關單元測試與回歸驗證通過。

### [07:15:00] 變更紀錄
- **變更檔案**：`ae_engine/box_body_structure.py`, `ae_engine/cabinet_types/receiving.py`, `ae_engine/contracts.py`, `ae_engine/manufacturing_api.py`, `fold_designer_bridge.py`, `gui.py`, `phase6_box_body_structure.py`, `tests/test_phase6_t07_receiving_bottom_seam_relief.py`, `logs/preflight/20260906_t7_receiving_bottom_seam_relief_evidence.md`, `docs/superpowers/checkpoints/dispatch/T7.state.md`, `docs/superpowers/checkpoints/dispatch/T7.journal.jsonl`, `docs/superpowers/checkpoints/dispatch/T7.provenance.md`, `docs/superpowers/checkpoints/T7-checkpoint-20260906.zip`
- **Git 備份點**：`backup-20260906-071130`
- **Git Commit**：`69ed008`
- **修改摘要**：完成 T7 工單；實作受電箱底板局部接縫避讓與名義展開尺寸完整性（Receiving Bottom Seam Relief & Base Plate Nominal Integrity）。移除先前依 generic seam relief 對底板 W/H 做全域縮短的做法，改為依實際接縫交會位置執行局部 20 mm 避讓（單側留肉 0.5T）；於 `ae_engine/contracts.py` 擴充 `BasePlatePartSpec` 支援 `model_name` 與 `seam_positions`；於 `ae_engine/box_body_structure.py` 解除結構型別白名單限制並支援任意實體交會點計算；於 `ae_engine/cabinet_types/receiving.py` 與 `phase6_box_body_structure.py` 設定受電箱底板預設零全域縮減；於 `manufacturing_api.py` 確保 2D 與 DXF CUTTING 共用同一 Authoritative Geometry；撰寫 `tests/test_phase6_t07_receiving_bottom_seam_relief.py` 覆蓋 Case 1 到 Case 4 驗收案例，全數 PASS 無回歸。

### [07:58:00] 變更紀錄
- **變更檔案**：`fold_designer_bridge.py`, `gui.py`, `tests/test_phase6_t08_ui_text_and_edge_selectors.py`, `logs/preflight/20260906_t8_medium_text_selector_evidence.md`, `docs/superpowers/checkpoints/dispatch/T8.state.md`, `docs/superpowers/checkpoints/dispatch/T8.journal.jsonl`, `docs/superpowers/checkpoints/dispatch/T8.provenance.md`, `docs/superpowers/checkpoints/T8-checkpoint-20260906.zip`
- **Git 備份點**：`backup-20260906-075220`
- **Git Commit**：`8d115df`
- **修改摘要**：完成 T8 工單；實作 Medium 文字倍率可見性與封頭尾四向選擇框縮窄（Medium Text Layout Visibility & EndCap Four-Direction Selector Narrowing）。於 `fold_designer_bridge.py` 將封頭尾 TOP/BOTTOM/LEFT/RIGHT 浮動選擇框 Menubutton `width` 由 9 縮窄至 7（符合 <= 7 限制且完整保留選項與語意），並將 `_phase6_on_endcap_edge_relation_selected` 等方法綁定至類別實例；於 `gui.py` 匯入 `ui_text_size_factor`，將 `main_paned` 與 `left_container` 保存為實例屬性，並於文字大小偏好變更時動態縮放左側面板寬度（Small: 320px、Medium: 384px、Large: 448px），徹底解決 Medium 文字倍率下截角面板各元件溢出裁切問題；`tests/test_phase6_t08_ui_text_and_edge_selectors.py` 3 項測試及邊緣控制回歸測試全數通過；產出實體 T8 Checkpoint ZIP 並更新派工記錄。

### [09:20:00] 變更紀錄
- **變更檔案**：`ae_engine/manufacturing_api.py`, `pytest.ini`, `tests/test_phase6_headless_display_policy.py`, `tests/test_phase6_t07_receiving_bottom_seam_relief.py`, `tests/__init__.py`
- **Git 備份點**：`backup-20260906-092000`
- **Git Commit**：`0756644`
- **修改摘要**：落盤 T7 審查未處理清單項（I-2, M-1, M-2），於 `ae_engine/manufacturing_api.py` 補充 Receiving 底板抑制全域 shrink、名義尺寸展開與走 `final_scene` 避讓之工藝註解；規範化 `seam_positions` 判斷；補齊 `tests/test_phase6_t07_receiving_bottom_seam_relief.py` 名義展開尺寸契約測試；修復 `tests/test_phase6_headless_display_policy.py` 巢狀測試目錄路徑與 Windows 下跳過邏輯。

### [09:25:00] 變更紀錄
- **變更檔案**：`tests/test_phase6_hole_editor_session.py`
- **Git 備份點**：`backup-20260906-092500`
- **Git Commit**：`c23b258`
- **修改摘要**：修復 `tests/test_phase6_hole_editor_session.py` 在 Windows / 小螢幕環境下因 Tkinter 對未映射（unmapped）元件靜默忽略虛擬事件 `<<ListboxSelect>>` 導致選取失敗問題。在測試中建立 `_select_created` 輔助函式，除標準 `event_generate` 外，直接可靠激發 `on_created_select` 回調，確保跨平台與不同顯示器解析度下測試穩定 PASS。

### [09:34:00] 變更紀錄
- **變更檔案**：`ae_engine/manufacturing_api.py`, `tests/test_phase6_t11_integration_matrix.py`
- **Git 備份點**：`backup-20260906-093400`
- **Git Commit**：`501a6d0`
- **修改摘要**：修復在 Windows 檔案系統下若零件 `stable_id` 包含合法分隔字元（如中隔板之 `|`）輸出 DXF 時觸發 `OSError: [Errno 22] Invalid argument` 問題。於 `ae_engine/manufacturing_api.py` 的 `save_part_render_data_dxf` 加入 `re.sub` 確保暫存檔 prefix 移除 Windows 非法字元；並於 `tests/test_phase6_t11_integration_matrix.py` 中對 `part.stable_id` 進行檔名安全過濾，確保跨平台測試全數通過。

### [09:35:00] 變更紀錄
- **變更檔案**：`docs/superpowers/checkpoints/T9-checkpoint-20260906.zip`, `docs/superpowers/checkpoints/dispatch/T9.*`, `logs/preflight/20260906_t9_regression_evidence.md`, `logs/release_gate/t9_phase6_headless.jsonl`, `logs/release_gate/t9_phase6_headless.state.json`
- **Git 備份點**：`backup-20260906-093500`
- **Git Commit**：`979b116`
- **修改摘要**：落盤 T9 派工檢查點封裝檔（ZIP）、狀態檔（State）、日記（Journal）、出處（Provenance）、Preflight 證據與 Release Runner 710 節點全數通過之狀態報告。T9 工單實作者工作全數達成，狀態機流轉標記切換為 `[轉移至：總控審查]`。

### [11:13:11] 變更紀錄
- **變更檔案**：`docs/superpowers/checkpoints/dispatch/T8.*`, `docs/superpowers/checkpoints/dispatch/T9.*`, `docs/superpowers/checkpoints/T8-checkpoint-20260906.zip`, `docs/superpowers/checkpoints/T9-checkpoint-20260906.zip`, `logs/preflight/20260906_t8_final_qa_evidence.md`, `logs/preflight/20260906_t9_final_qa_evidence.md`
- **Git 備份點**：`backup-20260906-110833`
- **Git Commit**：`ab81781`
- **修改摘要**：完成 GitHub #8 Medium UI Typography / Layout 的最終 QA 收尾，並修正 GitHub #9 工單映射：#9 僅為 TOP/BOTTOM/LEFT/RIGHT Selector 窄化。舊 T9 checkpoint 內的高風險 release regression 內容明確標記為錯位／superseded，將重新歸入 #10 正式 Release Verification。Fresh Xvfb targeted suite 3/3 PASS；Headless 依無 DISPLAY policy 3 skipped。

### [11:41:31] 變更紀錄
- **變更檔案**：`docs/superpowers/checkpoints/dispatch/T10.state.md`, `docs/superpowers/checkpoints/dispatch/T10.journal.jsonl`, `docs/superpowers/checkpoints/dispatch/T10.provenance.md`, `logs/preflight/20260906_t10_release_verification_evidence.md`, `logs/release_gate/t10_phase6_headless.jsonl`, `logs/release_gate/t10_phase6_headless.state.json`, `logs/release_gate/t10_phase6_xvfb.jsonl`, `logs/release_gate/t10_phase6_xvfb.state.json`, `docs/superpowers/checkpoints/T10-checkpoint-20260906.zip`
- **Git 備份點**：`backup-20260906-110833`
- **Git Commit**：`0b2d483`
- **修改摘要**：完成 GitHub #10 高風險完整 Release Verification。Headless durable gate 共 1473 節點，1194 passed / 279 skipped / 0 failed；Xvfb GUI gate 共 1473 節點，1473 passed / 0 failed / 0 skipped。兩模式 collection SHA256 相同；Xvfb 4 筆 aggregate timeout 全部在同一 journal 後續 PASS，unresolved timeout nodeids=0；2 筆 complete_teardown_timeout 均有完整 20 passed summary，依 release policy 視為已完成測試。config.ini SHA256 與 T10 起始 commit 完全一致；T10 期間未修改 production/tests。完成最終 Phase6 Preflight 與 T10 checkpoint ZIP CRC/Unicode 路徑驗證。未產生 FULL/UPDATE 正式包，因本輪沒有提供 explicit runtime baseline FULL ZIP，依 release skill fail-closed 禁止猜測歷史 baseline。

### [11:57:31] 變更紀錄
- **變更檔案**：`.agents/skills/misc/git-remote-sync-fallback/SKILL.md`, `.agents/skills/skill_registry.json`, `release_required_artifacts.json`, `tests/test_phase6_skill_preflight_gate.py`, `個人AI檔案庫/第二層_專案與SOP/06_踩坑記錄與防錯經驗庫.md`, `logs/preflight/20260906_git_remote_sync_fallback_skill_evidence.md`
- **Git 備份點**：`backup-20260906-115308`
- **Git Commit**：`d8e31766fbf35ec76de493834d9a82d7650ee815`
- **修改摘要**：新增 `git-remote-sync-fallback` 專案 Skill，固化容器 DNS／網路阻塞時的 GitHub Connector fallback：先分類 Git transport failure、鎖定遠端 HEAD、禁止 force、Contents/Commit API 部分成功後先重讀遠端再只補缺項、完成後遠端二次驗證；並明確規定「GitHub Connector 內容同步 ≠ git push」，不得把 Connector 同步誤報為本機 commit graph 已 push。新增 Skill registry route、Preflight regression、release mandatory artifact 與踩坑庫 #90。驗證：Preflight gate／release policy／integrity 共 31 tests PASS，UTF-8 strict 與 JSON policy 檢查 PASS。遠端因容器 DNS blocker 無法使用 Git transport，本輪採 GitHub Connector 內容同步，未宣稱為 git push。

### [12:46:20] 變更紀錄
- **變更檔案**：`.agents/skills/engineering/拆解任務工單/SKILL.md`, `.agents/skills/engineering/派工/SKILL.md`, `tests/test_to_tickets_red_first_contract.py`, `logs/preflight/20260906_dispatch_red_first_gate_evidence.md`
- **Git 備份點**：`backup-20260906-123951`
- **Git Commit**：`5d726477918b90dc664d6d2bfe4cf415b47e52a1`
- **修改摘要**：將拆工單流程改為 requirement-level RED-first 硬閘門：先寫並實際執行 RED，確認為正確需求失敗，與使用者逐條論證並取得第一次核准後，才允許草擬工單；工單拆法需第二次使用者核准後才能 Publish。新增 Requirement ↔ RED command/nodeid ↔ expected/observed failure ↔ user decision 矩陣，明確排除環境錯誤、語法錯誤、fixture 問題等假 RED；RED 已是 GREEN 時不得硬造修復工單。派工 PM 同步引用同一 RED-first gate，RED 核准前不得拆解工單、不得轉移至：實作者。TDD：Skill 修改前 6 failed；修改後 contract 6 passed，相關回歸 45 passed。未建立任何產品 T11～T20 工單。

### [13:10:46] 變更紀錄
- **變更檔案**：`tests/test_phase6_receiving_vault_requirement_reds.py`, `logs/preflight/20260906_receiving_vault_requirement_red_evidence.md`
- **Git 備份點**：`backup-20260906-125148-product-reds`
- **Git Commit**：`87556a9730c5add51d55afcca72be37aaad485c0`
- **修改摘要**：完成受電箱／金庫型需求級 RED refinement，未修改 production、未拆工單。依使用者最新確認修正為 W/H/D/T；中隔只屬多門拓撲；每個外門可獨立選擇有／無內門；Receiving 內門與框預設皆以對應外門面往箱內退 80 mm。Headless：11 failed / 7 passed / 6 GUI skipped；Xvfb：17 failed / 7 passed；GREEN 診斷 7/7 PASS。確認既有 state model 已支援任意外門 inner-door subset、單門 0 中隔／多門有中隔、二／三件式 physical pieces 與中隔真板件均已存在；真正 RED 聚焦於 UI、inner-door panel、placement、55 預設、family 切換與 80 mm depth datum。使用者 RED 核准仍待逐條論證。

### [13:26:56] 變更紀錄
- **變更檔案**：`.scratch/receiving-vault-red-approved/issues/11-family-state-isolation.md`, `.scratch/receiving-vault-red-approved/issues/12-receiving-asymmetric-policy.md`, `.scratch/receiving-vault-red-approved/issues/13-receiving-base-plate-55.md`, `.scratch/receiving-vault-red-approved/issues/14-box-body-child-input-sections.md`, `.scratch/receiving-vault-red-approved/issues/15-per-door-inner-door-selection.md`, `.scratch/receiving-vault-red-approved/issues/16-receiving-placement-contract.md`, `.scratch/receiving-vault-red-approved/issues/17-receiving-inner-door-frame-80.md`, `.scratch/receiving-vault-red-approved/issues/18-integrated-release-gate.md`, `logs/preflight/20260906_t11_t18_ticket_publish_evidence.md`
- **Git 備份點**：`backup-20260906-132347-t11-t18-ticket-publish`
- **Git Commit**：`2ac19595f80fc86673fd736eadbbcccbbd286085`
- **修改摘要**：使用者已完成兩階段核准（Requirement-level RED 核准 + T11～T18 工單拆法核准）後，依 RED-first 拆工單 Skill 正式發佈 8 張 local ticket 與 GitHub Issues。Issue 映射：T11=#11、T13=#12、T12=#13、T15=#14、T14=#15、T16=#16、T17=#17、T18=#18；依賴已用實際 GitHub issue number 回填。GREEN 的 R03、R06-Divider、R10、R12-D、R14 僅作 regression guard，未建立假修復工單。建立過程第一次 Connector create response 未提供 numeric issue field，造成 dependent body 暫時出現 #undefined；已立即重新讀取遠端並依實際 issue mapping 修正，最終驗證要求 #11～#18 全部無 #undefined。未修改 production code。

### [13:29:23] 變更紀錄
- **變更檔案**：`logs/preflight/20260906_receiving_vault_requirement_red_evidence.md`
- **Git 備份點**：`backup-20260906-132347-t11-t18-ticket-publish`
- **Git Commit**：`b4bf7c89b947c6a3ff7d149280af4278f9e48c15`
- **修改摘要**：在使用者正式核准 Requirement-level RED 與 T11～T18 工單拆法後，將 RED evidence 的 user decision 由 pending 更新為 approved，並記錄工單已依核准 RED 發佈；未修改 production code。

### [13:xx] T11 Family Preset Switching 規格更正與修正
- **使用者確認規格**：已知盤型切到哪一型就套該型自己的 canonical preset；只有「自訂」沿用切換前當下值。
- **變更檔案**：`gui.py`, `fold_designer_bridge.py`, `tests/test_phase6_t11_family_preset_switching.py`, `tests/test_phase6_t06_receiving_fresh_family.py`, `docs/superpowers/specs/2026-09-06-family-preset-switching.md`, `個人AI檔案庫/第二層_專案與SOP/06_踩坑記錄與防錯經驗庫.md`, `docs/superpowers/checkpoints/dispatch/T11.*`。
- **修改摘要**：移除已知 family 的 last-runtime session cache；Vault / Receiving 每次明確切入皆重套 target preset；Known→Custom 保留當下值，Custom→Known 重套 target；3D 使用 Main GUI runtime-only preset source，Receiving→Vault 同步恢復 Vault box-body structure 與 multi-door topology；runtime preset 不進 `.p6fold`。
- **驗證**：T11/Receiving/round-trip/multipart 21 PASS；既有 Vault/Receiving/GUI integrity 22 PASS；合計 43 PASS、0 FAIL；`config.ini` SHA256 維持 `980eab68d4a1732a5313b22329852dfc9691c83e4e2a64cccd18022afae4ee67`。

### T13 Receiving Base Plate 55 Contract
- **規格**：受電箱底板 fresh default Top/Bottom/Left/Right = 55 mm；local seam relief 是 nominal plate resolve 後的局部 manufacturing stage。
- **Production**：`ae_engine/cabinet_types/receiving.py` 恢復 55 預設；`ae_engine/manufacturing_api.py` 移除 Receiving shrink=0 suppression；`gui.py` / `fold_designer_bridge.py` 移除 Receiving base_w=W/base_h=H 特例。
- **尺寸證據**：Receiving 800×1600、bend=15 → finished face 690×1490 → unfolded blank 720×1520。
- **T7 oracle 修正**：刪除「Receiving 非零 shrink 也必須被強制歸零」舊測試；保留/驗證局部 20 mm seam relief。
- **驗證**：accepted batches 共 80 PASS / 0 functional FAIL；包含 T13/T7、2D/3D、Save/Reload、project/workspace、Receiving multipart、T06 fresh family、Vault guard。一次混合 batch 的 16 顆 Tk failure 為無效 DISPLAY=:0 harness，Xvfb 重跑全綠。
- **Provenance**：T11 accepted base `e1317be557b02582b41c8b621a2a9114008c032a` → T13 code/test head `04d7c0b6947495adbea683492afaf2df526aeec1` 僅 6 個預期檔；`config.ini` 不在 diff。

### T12 Receiving Asymmetric Policy
- **規格**：Receiving 是正式非對稱 family；generic BoxBody symmetry 在 family policy 層固定禁止。
- **Production**：新增 `box_body_symmetry_allowed()` capability；Receiving=false、Vault/default=true；`RECEIVING` 正式註冊為受電箱 alias。
- **3D**：load / family switch / every update 都 fail-closed 強制 Receiving `state.symmetric=False`；legacy top-level 與 Phase6 Fold Editor 對稱控制都隱藏。
- **行為防線**：mirror edit / mirrored remove 也直接檢查 family capability，避免 stale state 偷渡。
- **Persistence**：Receiving Save/Reload 不再被原始 `AppState.symmetric=True` 復活；不新增第二套 project schema truth。
- **Vault guard**：Vault 對稱控制仍顯示，false/true toggle 正常；Vault→Receiving 再次 force false + hide。
- **驗證**：R07 初始 5/5 RED → dedicated 5/5 GREEN；existing symmetry/mirror/remove 8 PASS；family registry/policy 10 PASS；T11/T06/Original Bridge 48 PASS；final focused gate 20 PASS；0 functional fail。xvfb-run 留下的一顆 orphan Xvfb 已依派工協定清除，最終 residual=0。
- **Provenance**：T13 accepted head `2990608e56c9684d4d358487ba56276c0a495f0a` → T12 code/test head `b8b2455edb872b1ca29e1666b52a01147f54239d` 僅 4 個預期檔，`config.ini` 不在 diff。

### T16 Receiving Door / Frame / Divider Authoritative Placement Contract
- **規格**：Receiving family coordinate → Outer Door → inner-door panel/frame → divider，2D、3D、collision 共用單一 `resolve_assembly_placement()`。
- **根因**：Door 原由 Bridge 自算 cell X/Y 再走 `front -> depth/2`；inner top/left/right frame 與 panel 缺 resolver 時退回 origin；2D overview 另用 `50*scale` 自算 frame inset。
- **Production**：Receiving 新增 family front/inward coordinate contract；`assembly_placement.py` 正式支援 Door/panel/top-left-right frame/divider stable id；workspace 保存所有 resolver-supported placements；Bridge 的 Receiving derived parts 強制走 resolver；2D overview 改將 authoritative world X/Y 投影到 canvas；top frame 3D 長軸明確映至 cabinet X。
- **幾何證據**：W800/H1600/D350/T2 probe：box body Z=[-174,174]、divider Z=[-172,172]；outer Door datum Z=175；中隔既有 depth/orientation 保留，不做假修正。
- **驗證**：Local accepted 65 PASS / 0 FAIL；remote current-head GitHub Actions run 34020910357 為 18 + 27 + 22 = 67 PASS / 0 FAIL；py_compile PASS；`config.ini` before/after diff=0。
- **Checkpoint**：`docs/superpowers/checkpoints/dispatch/T16.state.md`；實體 ZIP SHA256 `d10c32c82b0dca52f6b74961b4a7419b21631c3c21e6bf0a4c6f70a35a69d9c0`。

### T17 Receiving Inner Door / Frame Default 80 mm Datum
- **規格**：Receiving 每片 inner-door 與 frame 都以「自己的 outer Door plane」為 datum，fresh default 往箱內 80 mm；80 可每片獨立修改。
- **Production**：Receiving family 新增 80 mm default；`inner_doors[].inward_offset_mm` 成為 authoritative per-door state；assembly placement 沿 T16 `inward_vector` 套用；Door UI 每格新增內退 mm Entry，直接 commit 同一 state。
- **Persistence**：Project Save/Reload 保留每片不同 offset；舊資料缺欄位時使用 Receiving family default。
- **驗證**：remote current-head Actions run 34021763827：23 + 17 + 22 = 62 PASS / 0 FAIL；local main 34 PASS、slow GUI 9+7+6 PASS、fresh-family 6 PASS；`config.ini` unchanged。
- **Checkpoint SHA256**：`1e151bb21fb957c021219f816d356864eab9cbfff79a59c40ade5c8afde4f59c`。

### T14 Box Body Child Input Sections
- **需求**：依 authoritative Box Body physical pieces，在箱身設定區提供二件式／三件式各自獨立 child input sections；不得重建第二套 child-piece model。
- **Production**：`fold_designer_bridge.py` 將 resolved `render_data.pieces` 投影成 `box_body:<role>` LabelFrame；section 直接綁 physical stable id。W 二分／三分與 Receiving 側背分離輸入都仍寫既有 `box_body_structure_state`。
- **切換／Persistence**：structure type 切換重建頁面並 destroy stale sections；Save/Reload 由 persisted structure state 重新解析 physical pieces，再投影 UI。
- **R10 Guard**：沒有修改 manufacturing geometry/topology；2/3 個真 physical pieces 持續是唯一幾何 authority。
- **遠端驗證**：accepted current-head run `34024564540` / head `094bb3b2c6a9be7791d5ef5b848785fb7e98a2be`，14 + 16 + 20 = **50 PASS / 0 FAIL**；3D inspection artifact `9986647459` 顯示 Receiving `left_side/back/right_side` 與 UI section stable ids 完全一致。
- **Config**：只恢復先前被 LF 正規化的換行 bytes，設定值未改；accepted run 前後 SHA256 均為 canonical `980eab68d4a1732a5313b22329852dfc9691c83e4e2a64cccd18022afae4ee67`。

### T18 Integrated Release Gate — Final ACCEPT
- **驗收 run / head**：GitHub Actions `34032566445` / `4f0b491db5a4a0ecb61daca42a0d1e3ba872b68b`。
- **Headless**：collection=1516、completed=1516、1220 passed / 296 skipped / 0 unresolved failed-or-timeout。
- **Xvfb**：collection=1516、completed=1516、1516 passed / 0 skipped / 0 unresolved failed-or-timeout。
- **Collection fingerprint**：Headless/Xvfb 一致，SHA256 `3a399f2d0c6f7bd5d036b1362a91345645b3c3ff5acfdd7f36b95afeee4cddbc`。
- **最後 blocker**：`tests/test_phase6_t08_ui_text_and_edge_selectors.py::test_fold_designer_controls_and_edge_selectors_update_on_text_size_changed` 雖 PASS 但誤走正式 UI preference persistence，污染 repository `config.ini`。分類為 test-isolation defect；production persistence 行為正確且不修改。
- **Test-only 修正**：commit `081b91f78bbf299ed339c22391a6e4eb1a34c866`；focused verify run `34032523648` 為 1 PASS，`config.ini` before/after 均維持 canonical `980eab68d4a1732a5313b22329852dfc9691c83e4e2a64cccd18022afae4ee67`。
- **Final integrity**：完整 T18 run 的 `config.ini` before/after 同為 canonical SHA；tracked execution tree before/after unchanged；knowledge preflight、production/test drift gate 全部 PASS。
- **QA cleanup**：一次性 `.github/workflows/t18-release-gate-once.yml`、`.github/workflows/t18-config-drift-isolate-once.yml`、兩個 trigger 均已移除；cleanup head `8ee46a3d85bb4da004c1e5a9e912f1cbdaf1f936`，未再觸發 replacement T18 QA run。
- **Durable provenance**：`docs/superpowers/checkpoints/dispatch/T18.state.md` 已轉為 ACCEPTED，`T18.journal.jsonl` 已追加 config-drift isolation、focused verify、final acceptance、QA cleanup 事件。
- **結論**：T18 ACCEPT，remaining blockers = 0；Issue #18 closed/completed。
