looaeedr/whd/修改日誌/20260905.md

### [20:00:00] 變更紀錄
- **變更檔案**：`.agents/skills/engineering/phase6-release-packaging/SKILL.md`, `修改日誌/20260905.md`
- **Git 備份點**：`backup/20260905-2000-phase6-release-gate`
- **Git Commit**：`1a0a955f23b86faf3d0873b2e68aac4c2141c3a0`
- **修改摘要**：調整 Phase6 出包規則；正常情況下打包後不再重跑完整 GUI gate，改以 ZIP/CRC/UTF-8/逐檔 SHA256、pristine extraction 與來源樹一致性確認交付物等同已驗證來源。只有封裝流程改變執行環境或交付內容時，才追加針對風險的 package GUI Smoke。

### [23:22:00] 變更紀錄
- **變更檔案**：`docs/superpowers/specs/2026-09-05-2d-3d-receiving-box-integrity-design.md`, `修改日誌/20260905.md`
- **Git 備份點**：`backup/20260905-2322-before-spec-log`
- **Git Commit**：`43223ef4f2dbac444c8fe50174ec3ea80acb1e39`
- **修改摘要**：將 5.2 大規模重構的座標演算法遷移風險與漸進式替換／完整 Headless + GUI Gate 門檻，以及 5.3 完整 workspace snapshot 的互動期效能風險、Confirm 凍結、避免每幀序列化與後續 diff/lazy 策略，正式納入受電箱 2D／3D 一致性規格。
