looaeedr/whd/修改日誌/20260810.md

### [22:54:15] 變更紀錄
- **變更檔案**：
ersion.txt`n- **備份檔名**：BACKUP/20260810-225300-version.txt`n- **修改摘要**：完成 
ew-engine 合併至 master，更新版本號至 
0.0.13 並建立 Release Tag 
0.0.13 推送至遠端伺服器。
