looaeedr/whd/修改日誌/20260811.md

### [18:56:00] 變更紀錄
- **變更檔案**：`基準檔/開孔/AS&VS.dxf`, `基準檔/開孔/插座盒90X50.dxf`
- **備份檔名**：`BACKUP/20260811-185557-AS&VS.dxf`, `BACKUP/20260811-185557-插座盒90X50.dxf`
- **修改摘要**：依據《加工層分類與定義.md》規範，將 `基準檔/開孔/` 目錄下的 DXF 檔切削開孔輪廓調整為標準 `CUTTING` 加工層（綠色 Color = 3），輔助記號與標記調整為 `MARKING` 圖層（Color = 211），檢查尺寸調整為 `CHECK` 圖層（黃色 Color = 2）。
