looaeedr/whd/修改日誌/20260816.md

### [22:51:30] 變更紀錄
- **變更檔案**：`tests/test_ae_geometry_integration.py`, `tests/test_door_indicator_layout_regression.py`, `tests/test_endcap_corner_relief.py`, `tests/test_endcap_user_feature_preview.py`, `tests/test_gui_structural_rendering.py`, `tests/test_hole_editor_overlay_contract.py`, `tests/test_scene_secondary_render_regression.py`, `tests/test_unified_hole_editor_contract.py`, `tests/test_unified_hole_reference_ui.py`
- **備份檔名**：`BACKUP/20260816-222032-test_ae_geometry_integration.py`
- **修改摘要**：移除已被新架構（多門佈局、門板鏡向導出、箱身三面獨立編輯器）取代的過期測試檔案，全測試套件達到 100% 綠燈（260 passed）。
