looaeedr/whd/修改日誌/20260817.md

# 修改日誌

### [19:25:00] 變更紀錄
- **變更檔案**：	ests/test_clean_break_layout.py, 	ests/test_ae_geometry_integration.py, 	ests/test_base_plate_geometry.py, 	ests/test_indicator_box_geometry.py, 	ests/test_sheetmetal_drawing.py, docs/ae_docs_tmp/superpowers/plans/*.md
- **備份檔名**：BACKUP/20260817-191658-*, BACKUP/20260817-191755-sheetmetal_geometry.py, BACKUP/20260817-191813-test_clean_break_layout.py, BACKUP/20260817-191905-*, BACKUP/20260817-192117-*, BACKUP/20260817-192436-*, BACKUP/20260817-192444-*
- **修改摘要**：
  1. 完成 e-engine-clean-break 計畫：徹底移除根目錄舊有過渡 shims（e.py, contracts.py, manufacturing_api.py, sheetmetal_geometry.py, sheetmetal_features.py, sheetmetal_part_adapters.py, sheetmetal_drawing.py, hole_catalog.py）。
  2. 批量更新 	ests/ 所有測試模組改為直接引用權威核心封裝 e_engine.*。
  3. 修復測試中過時的 file-loader 及遺漏的 pytest import，並將 BACKUP/ 與 	mp/ 排除於 clean break 靜態掃描外。
  4. 執行完整回歸驗證：297 項測試全數通過（297 passed），py_compile 全數通過，真實 DXF 出圖煙霧測試（Door, Box Body, End Cap）與圖層（BEND, CHECK, CUTTING, MARKING）檢驗全數通過。
  5. 同步更新 docs/ae_docs_tmp/superpowers/plans/ 下所有計畫狀態為已完成。
