looaeedr/whd/修改日誌/20260819.md

### [20:59:10] 變更紀錄
- **變更檔案**：清理根目錄 25 個歷史修復腳本與臨時檔案（APPLY_CORNER_TYPE_PHASE6_FIX2.bat, apply_corner_type_phase6_fix2.py, APPLY_CORNER_TYPE_PHASE6_FIX3.bat, apply_corner_type_phase6_fix3.py, APPLY_CORNER_TYPE_PHASE6_FIX4.bat, apply_corner_type_phase6_fix4.py, APPLY_CORNER_TYPE_PHASE6_FIX5.bat, apply_corner_type_phase6_fix5.py, APPLY_CORNER_TYPE_PHASE6_FIX6.bat, apply_corner_type_phase6_fix6.py, APPLY_CORNER_TYPE_PHASE6_FIX7.bat, apply_corner_type_phase6_fix7.py, APPLY_ORIGINAL_FOLD_DESIGNER_PHASE6_FIX11.bat, apply_original_fold_designer_phase6_fix11.py, APPLY_VAULT_XY_FOLD_DESIGNER_PHASE6_FIX12.bat, apply_vault_xy_fold_designer_phase6_fix12.py, APPLY_FOLD_DESIGNER_OUTSIDE_DIMS_PHASE6_FIX13.bat, apply_fold_designer_outside_dims_phase6_fix13.py, APPLY_UNIFIED_PART_WORKSPACE_PHASE6_FIX14.bat, apply_unified_part_workspace_phase6_fix14.py, whd-corner-axis-grouped-reference-ui.patch, 新文字文件.txt, README_FIX2.txt, #U66f4#U65b0#U8aaa#U660e_FIX13_20260818.md, FIX13_#U6298#U5f4e#U5c3a#U5bf8#U8207#U5c01#U982d#U5c3e#U5b9a#U7fa9_20260818.md）
- **備份檔名**：BACKUP/20260819-205910-*
- **修改摘要**：依使用者指示清理專案根目錄不再需要的歷史修復腳本 (.bat, .py)、舊補丁 patch 檔、臨時說明文件與草稿檔，完成安全備份至 BACKUP/ 後自根目錄刪除。
