looaeedr/whd/修改日誌/20260831.md

### [20:50:34] 變更紀錄
- **變更檔案**：`AGENTS.md`, `.agents/skills/skill_registry.json`, `tools/phase6_skill_preflight.py`, `release_required_artifacts.json`, `基準檔/截角資料庫/README_母規則說明.md`, `基準檔/截角資料庫/certified_relief_rules.schema.json`, `基準檔/截角資料庫/certified_relief_rules.json`, `tests/test_phase6_skill_preflight_gate.py`, `docs/superpowers/verification/2026-08-31-skill-preflight-registry-gate.md`
- **備份檔名**：`BACKUP/20260831-204547-AGENTS.md`, `BACKUP/20260831-204547-release_required_artifacts.json`, `BACKUP/20260831-204547-README_母規則說明.md`, `BACKUP/20260831-204547-certified_relief_rules.schema.json`, `BACKUP/20260831-204547-certified_relief_rules.json`, `BACKUP/20260831-205034-phase6_skill_preflight.py`, `BACKUP/20260831-205034-skill_registry.json`
- **修改摘要**：建立 Phase6 Skill Preflight 三層強制鏈：AGENTS 啟動規則、machine-readable Skill Registry、自動 preflight CLI；同時擴充截角資料庫 STANDARD 母規則 schema/metadata，並將相關 gate、資料庫與 evidence 納入 release mandatory artifacts。
- **驗證命令**：`python tools\phase6_skill_preflight.py --task "OVERLAY release skill registry certified relief database gate" --changed-file AGENTS.md --changed-file release_required_artifacts.json --changed-file tools/phase6_skill_preflight.py --changed-file 基準檔/截角資料庫/certified_relief_rules.json --evidence docs/superpowers/verification/2026-08-31-skill-preflight-registry-gate.md`; `python -m pytest tests\test_phase6_skill_preflight_gate.py tests\test_certified_relief_registry_schema_v2.py tests\test_external_registry_runtime_reload.py tests\test_release_integrity_gate.py tests\test_phase6_release_packaging_policy.py tests\test_phase6_corner_3d_model_integrity_skill.py -q`

### [21:02:42] 變更紀錄
- **變更檔案**：`docs/superpowers/specs/2026-08-31-phase6-joint-graph-migration-spec.md`, `修改日誌/20260831.md`
- **備份檔名**：`BACKUP/20260831-210153-20260831.md`
- **修改摘要**：依 `PHASE6_組合尺寸截角與JointGraph_整合最高優先規格_20260831.md` 與目前程式盤點，新增 Joint Graph / 尺寸 / STANDARD 截角收斂實作規格，標示 ready-for-agent，整理問題、解法、user stories、implementation decisions、testing decisions、out of scope 與目前高風險差距。
- **驗證命令**：`python tools\phase6_skill_preflight.py --task "PHASE6 JointGraph OVERLAY WRAP corner 3D implementation spec" --changed-file docs/superpowers/specs/2026-08-31-phase6-joint-graph-migration-spec.md --evidence docs/superpowers/specs/2026-08-31-phase6-joint-graph-migration-spec.md`
