looaeedr/whd/修改日誌/20260903.md

# 2026-09-03 修改日誌

## GUI / 3D 效能知識固化

- 新增 `.agents/skills/engineering/phase6-gui-performance-integrity/SKILL.md`，固定 Scheduler 唯一 calculation executor、Transaction Guard 職責、GUI↔3D anti-echo、revision/transaction_id、set-if-changed、3D atomic initialization、DXF source/derived cache 分層、網路磁碟 `SOURCE_UNVERIFIED`、Save/Export 強制 flush、真 GUI 壓力 gate 與 durable checkpoint。
- `.agents/skills/skill_registry.json` 新增 `phase6-gui-performance` route；GUI 效能、live-sync、重算、DXF cache、debounce 與 `gui.py/fold_designer_bridge.py` 修改會自動要求 `phase6-gui-performance-integrity`。
- `AGENTS.md` 的 Skill Preflight 最低要求同步新增 GUI 效能 route。
- 全域踩坑庫新增 #77～#83：live-sync 重算風暴、DXF cache 分層、3D initialization revision、durable checkpoint、pytest cache 污染 pristine overlay、真 GUI 壓力 gate、release runner process-group cleanup race。
- `phase6-release-packaging` Skill 補強 durable checkpoint、父程序先退出仍需確認 process group cleanup、pristine FULL/UPDATE overlay 比對規則。
- 新增 `tests/test_phase6_gui_performance_knowledge.py`，以 regression 鎖住 registry/Skill/踩坑庫內容。
- `release_required_artifacts.json` 將新 Skill、知識 regression 與本日修改日誌列為 mandatory update files，避免後續 UPDATE 漏包。

## 不變項

- 本輪只修改 AI/流程知識、registry、測試與文件；未修改 Phase6 production geometry/runtime behavior。
- `config.ini` 不修改。

## 深模組效能架構深化實作／Release Runner 防錯

- 完成 Scheduler 唯一 calculation executor、GUI↔3D anti-echo/atomic init、derived cache owner、`SOURCE_UNVERIFIED` strict manufacturing gate，以及 Manufacturing → Collision 單向 contract 的 T01～T12 targeted/stress 收口。
- release 全回歸期間抓到並修正 `tools/phase6_release_test_runner.py --reset` 的 lock ordering：reset 現在先取得 journal run lock 才能刪除 journal/state；並以真 concurrent CLI regression 鎖住「持鎖時第二個 reset 不得改動原 journal」。
- 修正 legacy `SimpleNamespace` GUI handler fixture 未實作 `_request_phase6_update` 的測試契約落差；production 不新增 direct calculation fallback，保持 Scheduler 唯一 executor。
- 全域踩坑庫新增 #84～#85，並同步補強 `phase6-release-packaging` 與 `phase6-gui-performance-integrity` Skill。
- `config.ini` 保持不修改；本輪不改 Certified Registry、STANDARD、AssemblyJoint、INSERT／OVERLAY／INSERT_OVERLAY／包覆貼外等機械真值。

## 2026-09-03 20:31+08:00 — Release canonical baseline 更新
- Phase6 cumulative UPDATE canonical baseline 改為 `PHASE6_GUI_PERFORMANCE_KNOWLEDGE_FULL_20260903_124853.zip`。
- `PHASE6_FW_LINK_BUGFIX_FULL_20260823_212355(3).zip` 降為歷史 release 紀錄，不再是現行 packaging gate。
- 因 124853 baseline 已不存在舊 `skills/` 與 retired `tests/test_phase6_user_p6fold_live_sync.py`，現行 `update_cleanup_paths` 清空；未來只有新的刪除/搬移才新增 cleanup。
- `config.ini` 仍禁止進 UPDATE，且內容不得因此次 policy 遷移而修改。

### [20:52:44] 變更紀錄
- **變更檔案**：`DELIVERY_README.md`, `tests/test_phase6_semantic_doc_status.py`, `tests/test_traditional_chinese_handoff.py`, `docs/superpowers/verification/2026-09-03-delivery-readme-hardcode-risk.md`, `修改日誌/20260903.md`
- **備份檔名**：`BACKUP/20260903-205244-DELIVERY_README.md`, `BACKUP/20260903-205244-test_phase6_semantic_doc_status.py`, `BACKUP/20260903-205244-test_traditional_chinese_handoff.py`, `BACKUP/20260903-205244-20260903.md`
- **修改摘要**：降低 `DELIVERY_README.md` 固定檔名被後續代理誤當 mandatory artifact 或 Source of Truth 的風險；語意測試改由正式接手文件承載 current runtime guard，交付檔本身標註為歷史備忘。

### [21:03:01] 變更紀錄
- **變更檔案**：`AGENTS.md`, `docs/superpowers/verification/2026-09-03-dispatching-checkpoint-gate.md`, `修改日誌/20260903.md`
- **備份檔名**：`BACKUP/20260903-210301-AGENTS.md`, `BACKUP/20260903-210301-20260903.md`
- **修改摘要**：補強派工 Skill 實際執行硬閘門，要求總控驗收 PM/Worker/QA 角色標記、checkpoint path、journal/state path 與 resume command；缺任一項即視為未實際執行派工協定。

### [21:05:48] 變更紀錄
- **變更檔案**：`UPDATE/AGENTS.md`, `UPDATE/docs/superpowers/verification/2026-09-03-dispatching-checkpoint-gate.md`, `UPDATE/修改日誌/20260903.md`
- **備份檔名**：`BACKUP/20260903-210527-UPDATE-20260903.md`
- **修改摘要**：依使用者要求將本輪派工 checkpoint gate 變更同步複製到 `UPDATE/` 目錄，維持可覆蓋更新包的相對路徑結構；複製後以 SHA256 驗證 root 與 UPDATE 內對應檔案一致。

### [21:08:16] 變更紀錄
- **變更檔案**：`PHASE6_DEEP_MODULE_PERFORMANCE_FIX_UPDATE_20260903_204512/AGENTS.md`, `PHASE6_DEEP_MODULE_PERFORMANCE_FIX_UPDATE_20260903_204512/DELIVERY_README.md`, `PHASE6_DEEP_MODULE_PERFORMANCE_FIX_UPDATE_20260903_204512/docs/superpowers/verification/2026-09-03-delivery-readme-hardcode-risk.md`, `PHASE6_DEEP_MODULE_PERFORMANCE_FIX_UPDATE_20260903_204512/docs/superpowers/verification/2026-09-03-dispatching-checkpoint-gate.md`, `PHASE6_DEEP_MODULE_PERFORMANCE_FIX_UPDATE_20260903_204512/docs/superpowers/verification/2026-09-03-integrated-deep-module-update-dispatch-gate.md`, `PHASE6_DEEP_MODULE_PERFORMANCE_FIX_UPDATE_20260903_204512/tests/test_phase6_semantic_doc_status.py`, `PHASE6_DEEP_MODULE_PERFORMANCE_FIX_UPDATE_20260903_204512/tests/test_traditional_chinese_handoff.py`, `PHASE6_DEEP_MODULE_PERFORMANCE_FIX_UPDATE_20260903_204512/修改日誌/20260903.md`
- **備份檔名**：`BACKUP/20260903-210816-DEEP-AGENTS.md`, `BACKUP/20260903-210816-DEEP-DELIVERY_README.md`, `BACKUP/20260903-210816-DEEP-20260903.md`
- **修改摘要**：將 `PHASE6_DEEP_MODULE_PERFORMANCE_FIX_UPDATE_20260903_204512` 與本輪派工 checkpoint gate / DELIVERY_README 風險防線整合；保留 performance update 的 production、release policy 與封包資訊，只補入缺失的 SOP/evidence/tests 與日誌紀錄。
