looaeedr/whd/.scratch/dm5/journal.md

# DM5 Journal

- task_id: DIVIDER-FW-DEEP-MODULE-V1
- work_order: #55
- role: [當前角色：#55 實作者]
- branch: work/dm5-divider-deep-module-integration
- trusted_parent: work/dm4-divider-resolved-sinks@43629193dcd57c9194b15814e8ee210eedce10f1

## Dependencies
- #51 closed/completed
- #52 closed/completed
- #53 closed/completed
- #54 closed/completed

## Writeback RED / GREEN
- RED run 34239700844: 2 failed / 0 harness error.
- GREEN run 34239947942: 2 passed / 0 failed.
- Skill selfcheck 34240207687: terminal success.
- Traditional Chinese source gate: PASS.
- scan/tickets/dispatch structural checks: PASS.

## Authoritative writebacks landed
- .agents/skills/engineering/掃描深模組/SKILL.md
- .agents/skills/engineering/拆解任務工單/SKILL.md
- .agents/skills/engineering/派工/SKILL.md
- CONTEXT.md
- 個人AI檔案庫/踩坑庫/phase6_assembly_relief_pitfalls.md
- 個人AI檔案庫/第二層_專案與SOP/06_踩坑記錄與防錯經驗庫.md

## Combined Acceptance attempts
### Attempt 1
- run: 34240887879
- tested SHA: 59a2f4e1b92433c35847429e7d059fd2accc3fc2
- result: 196 passed / 2 failed
- config before/after: 980eab68d4a1732a5313b22329852dfc9691c83e4e2a64cccd18022afae4ee67
- classification: stale DM1 RED contract after DM3 moved final_material / relief_evidence into ResolvedDividerFinalGeometry.
- action: aligned DM1 durable guard with current canonical contract; production unchanged.

### Attempt 2
- run: 34241489389
- tested SHA: 663ac25399b5ad2c5a8f1237d118ff65058a337c
- Combined pytest: 198 passed / 0 failed
- config before/after: 980eab68d4a1732a5313b22329852dfc9691c83e4e2a64cccd18022afae4ee67
- source scan: INVALID_HARNESS because bare string search for 174 matched indicator-door color #9d174d.
- action: made numeric oracle scan token-aware; production unchanged.

### Final Combined
- run: 34241880494
- tested SHA: d7a2e1a0d6553dedf510a594ae015b1010b29c0d
- result: **198 passed / 0 failed / 0 error**
- Phase6 knowledge/skill preflight: PASS
- production compile boundary: PASS
- Divider deep-module source ownership scan: PASS
- config before: 980eab68d4a1732a5313b22329852dfc9691c83e4e2a64cccd18022afae4ee67
- config after:  980eab68d4a1732a5313b22329852dfc9691c83e4e2a64cccd18022afae4ee67

## Target drift pre-audit
- cleanup/2d-3d-sync HEAD before integration: 11192e3ac47251e99fe1d2760031dada96fde227
- relation: target is a pure ancestor of DM5 execution tree; no external target drift.
- non-force fast-forward is structurally available after final cleanup/drift audit.

## One-shot workflow cleanup
Removed after final terminal GREEN:
- .github/workflows/dm1-preflight.yml
- .github/workflows/dm1-red.yml
- .github/workflows/dm5-combined.yml
- .github/workflows/dm5-skill-selfcheck.yml
- .github/workflows/dm5-writeback-red.yml

## Post-QA drift audit
- tested SHA: d7a2e1a0d6553dedf510a594ae015b1010b29c0d
- cleaned execution head before final evidence docs: 6807c734c6037a4c86bbdd8bf460c9d28ee7d407
- delta after tested SHA: only five one-shot workflow removals + DM5 journal/checkpoint updates.
- post-QA production code delta: none.

## Integration
- target before integration: cleanup/2d-3d-sync@11192e3ac47251e99fe1d2760031dada96fde227
- ancestry check: target was a pure ancestor of DM5 head; behind_by=0 from target perspective.
- non-force update_ref(force=false): success.
- first production remote readback: cleanup/2d-3d-sync@6807c734c6037a4c86bbdd8bf460c9d28ee7d407
- execution branch remote readback: work/dm5-divider-deep-module-integration@6807c734c6037a4c86bbdd8bf460c9d28ee7d407
- these final journal/checkpoint commits are documentation-only; target will be fast-forwarded once more to the final durable evidence head before #55 closes.
