looaeedr/whd/.scratch/issue107/checkpoints/T1.md

# #107 / #108 T1 checkpoint
- role: T1 Implementer
- owning issue: #108
- target baseline: a37de3ad697ef225b711f6ea0eee86bf2b7712d4
- branch: fix/issue108-boxbody-parent-aggregate-20260911
- RED: 3 expected failures proving parent identity hijack + aggregate projection None
- GREEN focused: tests/test_issue96_corner_data_selection_lifecycle.py + tests/test_issue97_authoritative_unfold_view_adapter.py
- production changed: fold_designer_bridge.py only
- tests changed: issue96/issue97 legacy assertions replaced by approved Contract
- pending: exact-head remote QA; PM/QA acceptance; then #109
- blocked: none at checkpoint creation
- resume: read #108 + this checkpoint, then inspect exact-head QA for this branch
