looaeedr/whd/.scratch/issue107/checkpoints/T2.md

# #107 / #109 T2 checkpoint
- role: T2 Implementer
- owning issue: #109
- accepted base: 185fd413097701a77395da3746427ae7ab897584
- branch: fix/issue109-boxbody-parent-child-tree-20260911
- RED: 5 expected failures proving hierarchy projection/panel grouping missing
- GREEN: dedicated T2 + issue95/96/97 identity contracts
- production changed: fold_designer_bridge.py View hierarchy only
- manufacturing flat key authority unchanged
- pending: exact-head QA; QA review; then #110
- resume: read #109 + this checkpoint, inspect exact-head QA
