looaeedr/whd/.scratch/issue107/checkpoints/T3.md

# #107 / #110 T3 checkpoint
- role: T3 Implementer
- owning issue: #110
- accepted base: 01fe5c39ff32c7513e6e464f29f94423b46c4fe7
- branch: fix/issue110-shared-info-projection-20260911
- authority: existing resolve_operator_finished_dimensions + per-key profiles + render-data corner/unfold text
- production scope: shared display formatter + Corner Data info request/label only
- manufacturing geometry authority unchanged
- pending: exact-head QA; QA review; then #111
