looaeedr/whd/.scratch/issue107/checkpoints/T4.md

# #107 / #111 T4 checkpoint
- role: T4 Implementer
- owning issue: #111
- accepted base: 163dd5d6a9416887fb65b75d329ce56d62793236
- branch: fix/issue111-corner-data-grid-isolation-20260911
- authority: current gui.py renderer ownership + approved Grid Contract
- production scope: remove one local Corner Data draw_grid call only
- draw_grid implementation and unrelated callers guarded by AST invariants
- manufacturing geometry / DXF / info projection unchanged
- pending: exact-head QA; cleanup; drift audit; then #112
