looaeedr/whd/docs/superpowers/checkpoints/issue334-t1-green-candidate.md

# #334 T1 GREEN candidate

- Base production: `d88bf904317fb16744bfc644bb89ff7b405c435e`
- RED run: `35336197636`
- Minimal implementation commit: `b2e4babfb408fd67ffe501ea3919ee414144f150`
- Scope: shared dark Menu/Popup presentation only.
- Modified production owners: `fold_designer_bridge.py`, `gui_modules/parts/panels/door.py`, `gui_modules/editors/hole_editor_composition.py`.
- Callback/state/domain authority: unchanged.
- This commit exists to provide a normal Contents-API push event for the GREEN QA identity after the atomic Git-ref update did not immediately surface a workflow run.
