looaeedr/whd/docs/superpowers/checkpoints/issue335-t2-red.md

# #335 T2 RED trigger

- Production base: `4bdb0e0366b3accb983a25365cc7b29008a74544`
- Scope: top toolbar / right control layout presentation only.
- Expected RED: output controls are still a right-side `LabelFrame("輸出")`, visual controls still a `LabelFrame("3D 顯示")`, and global settings are packed before display controls.
