looaeedr/whd/docs/superpowers/checkpoints/issue336-t3-final-candidate.md

# #336 T3 final candidate

- Production base: `6f3dc763ac22a1f56a1fa80f817ae574ba0706a5`
- Expected RED: `35338152926`
- Production implementation: `88077f5366bc990974f0e3beb10f4a791ee429dd`
- Superseded layout assertions updated: `72cf40c6b00f8cb951210d54400abff01e6eece6`
- Previous Xvfb classification: **20 passed / 3 failed**, all three stale assertions expecting `part_var == 組合體`; no production failure.
