looaeedr/whd/docs/superpowers/checkpoints/issue337-t4-red.md

# #337 T4 RED trigger

- Production base: `43c701b08ae802789db4b501475697b0f2b966d7`
- Expected gap: shared ttk roles `Primary.TButton`, `Secondary.TButton`, `Selector.TMenubutton`, `Editable.TEntry`, `Readonly.TEntry` are not yet defined/assigned.
- Scope is presentation only; callback/state/domain authority is protected.
