looaeedr/whd/docs/superpowers/checkpoints/issue421-phase5-t0-journal.md

# Phase 5 / Issue #421 T0 Journal

## Authority

- MASTER_ID: `#413`
- TASK_ID: `#421 / T0`
- TARGET_X: `cleanup/2d-3d-sync`
- FROZEN_X_BASE_SHA: `396bfd96524a44a178c29bbefaf1b7c0437c119f`
- WORK_ORDER_BRANCH: `refactor/issue413-phase5-assembly-presentation-20260920`
- Requirement Authority: Phase 5 v1.7 accepted master #413
- Pre-spec #416 / PR #417: INVALID / not accepted task evidence
- T0 mode: characterization/evidence only; no runtime implementation

## Knowledge Preflight

Machine preflight was run before work-order branch creation and returned RC=0.

READ_SKILL: 截角資料入口收斂
READ_SKILL: 派工
READ_SKILL: issue-closure-gate
READ_SKILL: phase6-corner-3d-model-integrity
READ_SKILL: executable-continuity-controller
READ_SKILL: monitoring-remote-qa
READ_SKILL: long-log-context-safe-execution

READ_REFERENCE: 個人AI檔案庫/第二層_專案與SOP/06_踩坑記錄與防錯經驗庫.md
READ_REFERENCE: 個人AI檔案庫/第二層_專案與SOP/08_WHD截角資料與2D入口收斂規則.md
READ_REFERENCE: 個人AI檔案庫/踩坑庫/dm7_part_navigation_pitfalls.md
READ_REFERENCE: 個人AI檔案庫/第二層_專案與SOP/08_WHD技能建立與修改規則.md
READ_REFERENCE: 基準檔/截角資料庫/README_母規則說明.md
READ_REFERENCE: 基準檔/截角資料庫/certified_relief_rules.json
READ_REFERENCE: 個人AI檔案庫/踩坑庫/phase6_assembly_relief_pitfalls.md
READ_REFERENCE: 個人AI檔案庫/踩坑庫/executable_continuity_controller_pitfall.md
READ_REFERENCE: 個人AI檔案庫/踩坑庫/long_log_context_safe_execution.md

SUPPORTING_REFERENCE_READ: 個人AI檔案庫/踩坑庫/issue_closure_completion_pitfalls.md
SUPPORTING_REFERENCE_READ: 個人AI檔案庫/第二層_專案與SOP/09_X第二主分支與獨立工單鏈治理規格.md

## Execution Claim

- shared atomic claim ref: `claims/issue-421`
- worker: `looaeedr:chatgpt-gpt5.6-sol`
- work branch: `refactor/issue413-phase5-assembly-presentation-20260920`
- claim base: `396bfd96524a44a178c29bbefaf1b7c0437c119f`
- initial claim phase: `CLAIMED`
- branch-create guard: `EXECUTION_CLAIM_GUARD_GREEN`

## T0 Required Characterization

- exact symbol boundary / machine census
- top-level row source vs render-time BoxBody piece source
- DM7 vs `render_data.pieces` key-set relationship
- `box_body` absent + `box_body:*` present behavior
- Final Scene query/sink order
- formatter sources
- visibility fallback + BoxBody piece tri-state
- Structure Tree registry-empty entry paths
- refresh call sites
- mount/unmount paths
- legacy attribute readers/writers/dynamic getattr
- `_phase6_last_assembly_corner_dimension_texts` usage
- protected owner manifest
- right-side Assembly diagnostics out-of-scope proof

## State

```text
STATE=RUNNING
RUN_ID=RUN_NOT_CREATED
NEXT_ACTION=Create guarded T0 workflow and trigger exact work-order HEAD by push.
```
